HoldenLab/LifeHack/Main Body/Parts/Camera mount (With OptoSplit).stl

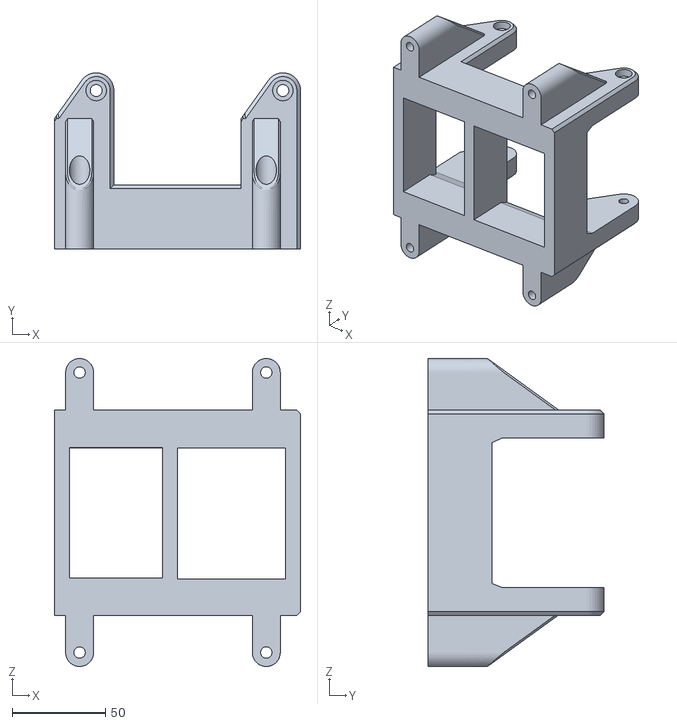
[picture p37: CAD file, 2020-11-02]
Main Body/Parts/Camera mount (With OptoSplit).stl
131.9 x 94.5 x 165.0
