HoldenLab/LifeHack/Main Body/Parts/Focus Shifter/Arduino Box/Arduino Box Bottom.stl

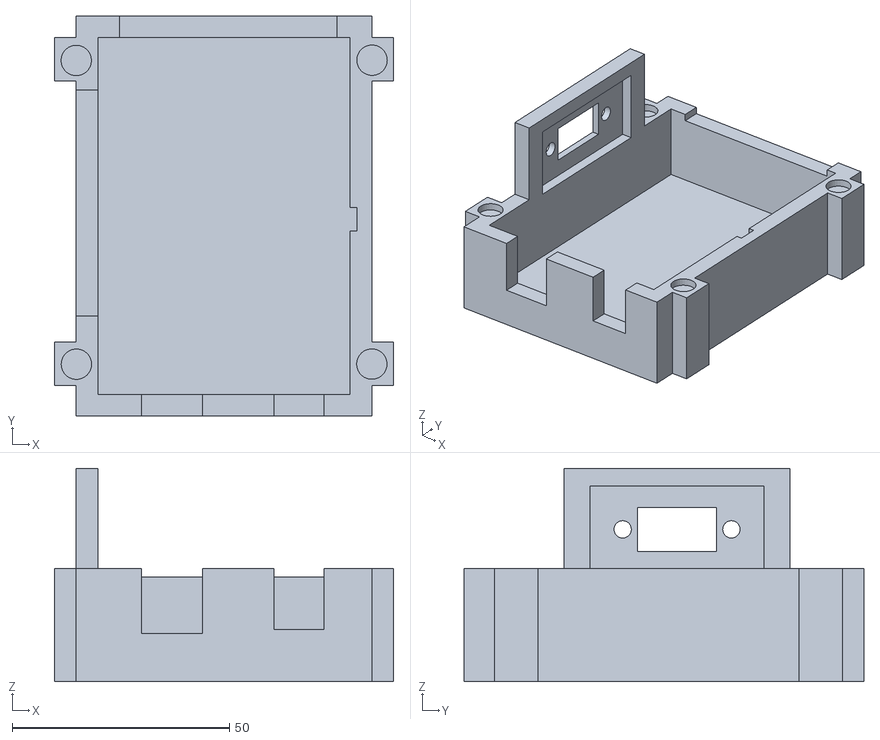
[picture p38: CAD file, 2020-12-13]
Main Body/Parts/Focus Shifter/Arduino Box/Arduino Box Bottom.stl
78.0 x 92.0 x 49.0
