HoldenLab/LifeHack/Main Body/Parts/Focus Shifter/Controller Box/Controller Box Bottom.stl

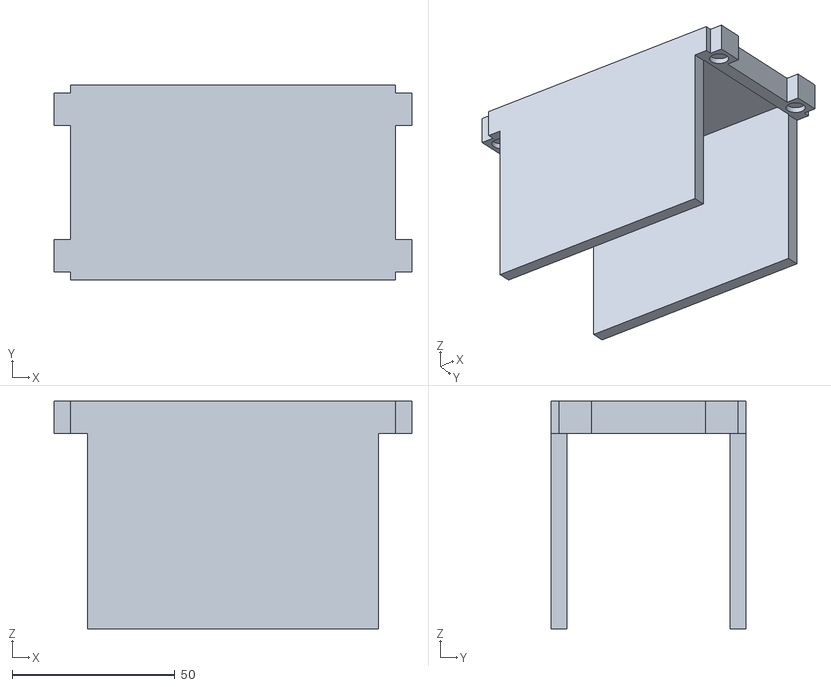
[picture p39: CAD file, 2020-12-13]
Main Body/Parts/Focus Shifter/Controller Box/Controller Box Bottom.stl
110.0 x 60.0 x 70.0
