HoldenLab/LifeHack/Excitation Module/Parts/Diode Laser Mount - 3D Print.stl

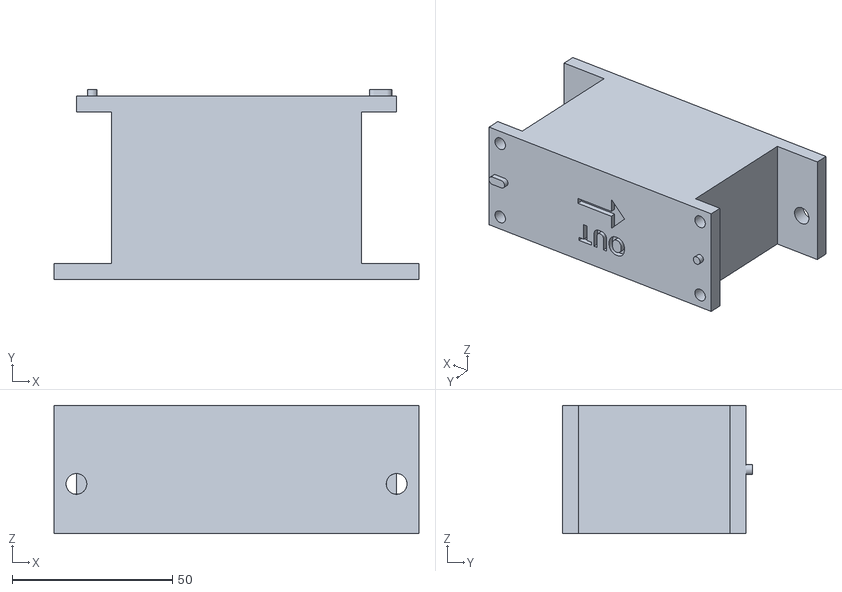
[picture p40: CAD file, 2020-10-29]
Excitation Module/Parts/Diode Laser Mount - 3D Print.stl
114.0 x 59.2 x 40.0
