HoldenLab/LifeHack/Incubation Box/Parts/Incubation-Chamber-Front-Middle-Door-Mount1.dxf

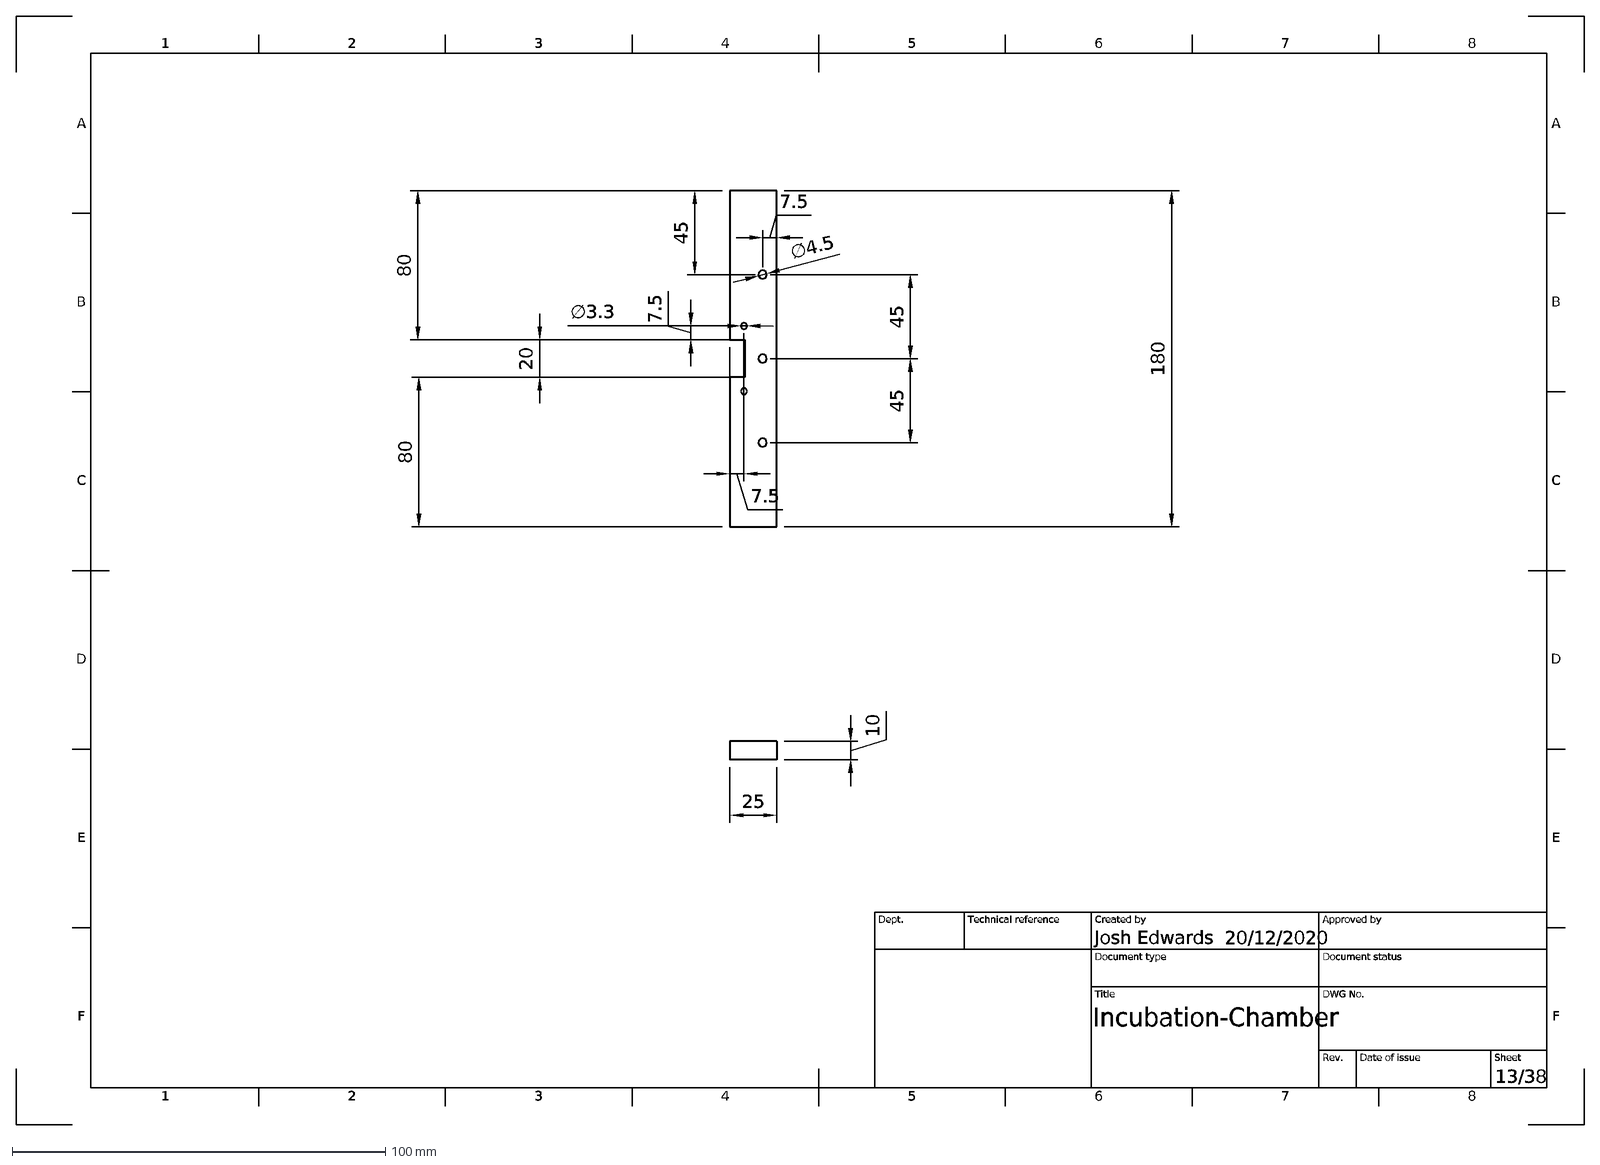
[picture p41: CAD file, 2020-12-22]
Incubation Box/Parts/Incubation-Chamber-Front-Middle-Door-Mount1.dxf
1
A
2
3
4
5
6
7
8
B
C
D
E
F
20/12/2020
13/38
Incubation-Chamber
Josh Edwards
Dept.
Technical reference
Created by
Approved by
Document type
Document status
Title
DWG No.
Rev.
Date of issue
Sheet
25
10
20
80
180
∅4.5
45
7.5
∅3.3
