HoldenLab/LifeHack/Excitation Module/Parts/Fiber Laser Mount - 3D Print.stl

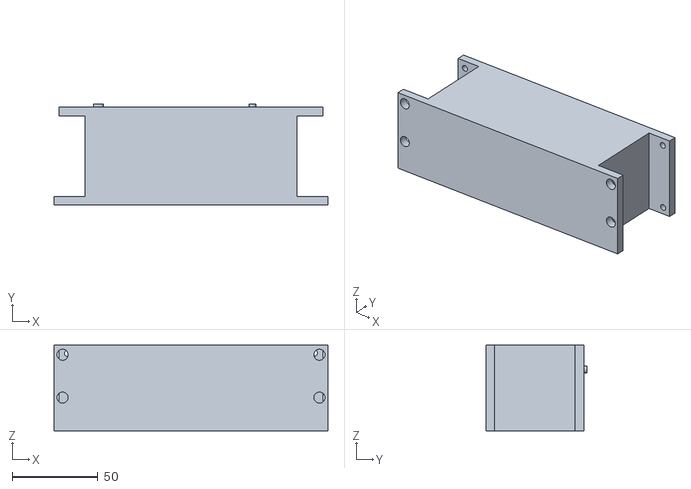
[picture p42: CAD file, 2020-10-29]
Excitation Module/Parts/Fiber Laser Mount - 3D Print.stl
160.0 x 59.2 x 50.0
