HoldenLab/LifeHack/Incubation Box/Parts/Incubation-Chamber-Left-Door-Mount3.dxf

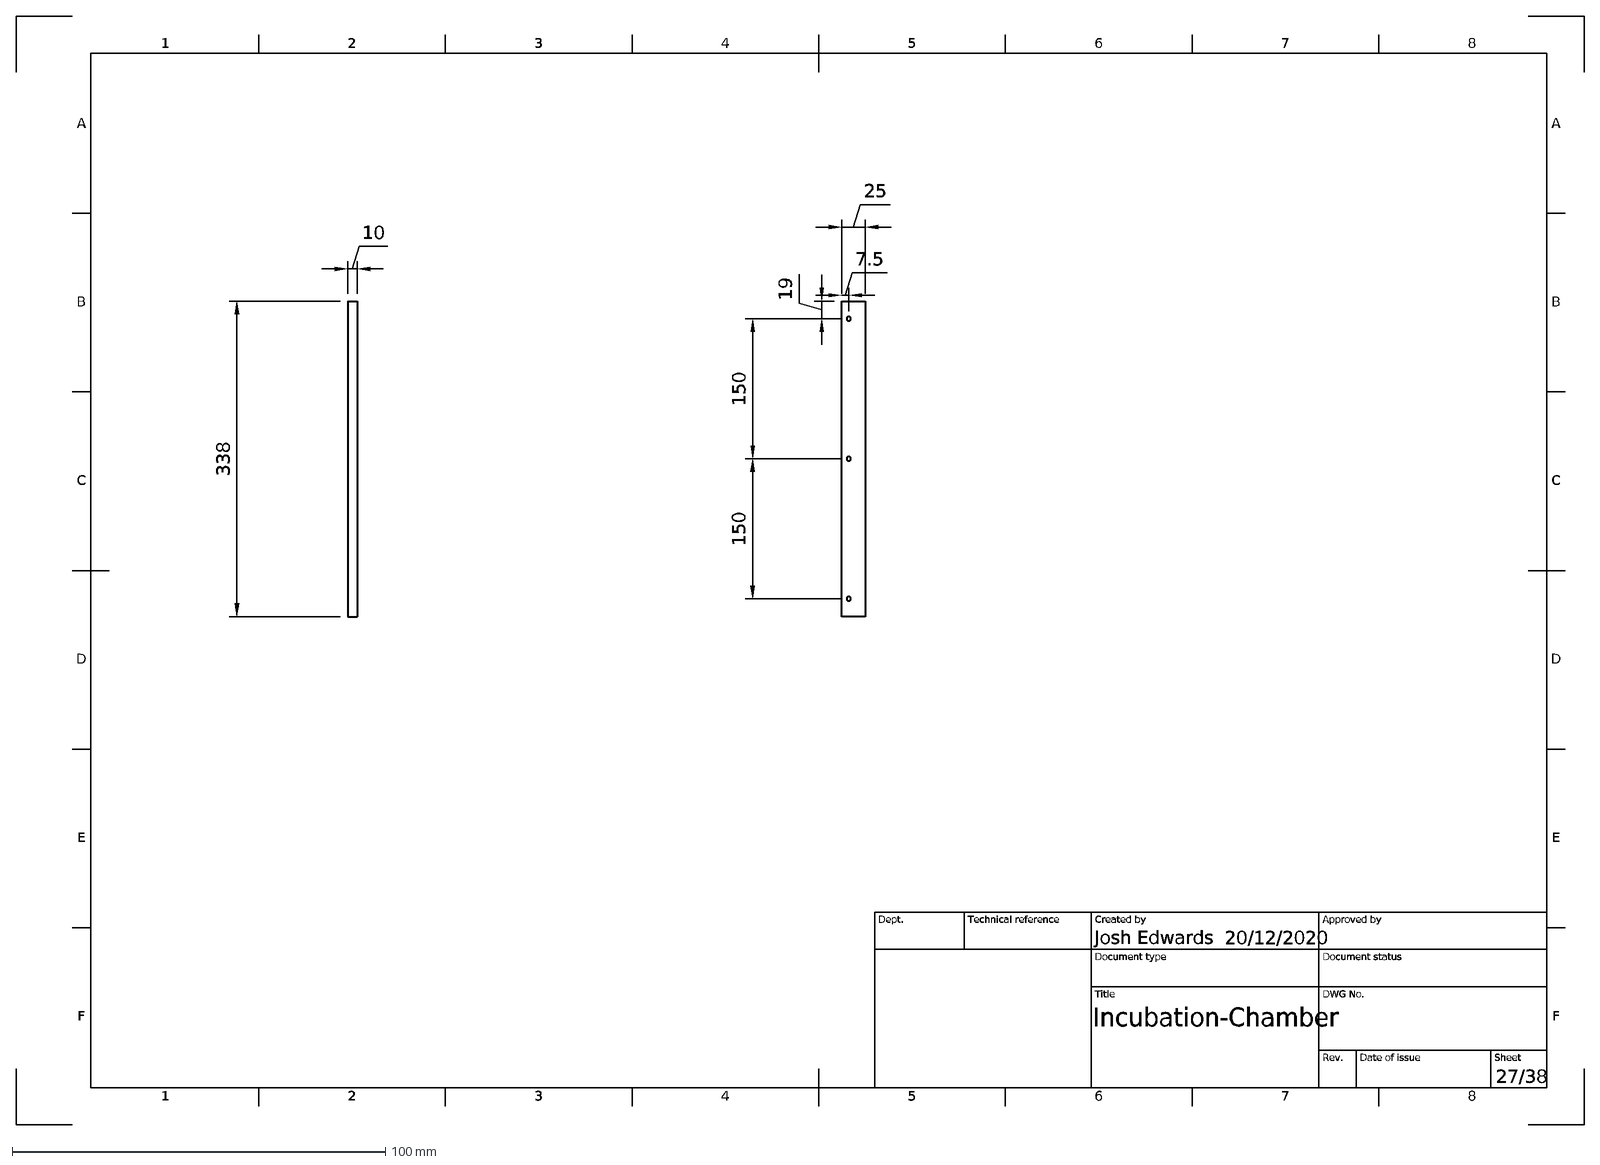
[picture p43: CAD file, 2020-12-22]
Incubation Box/Parts/Incubation-Chamber-Left-Door-Mount3.dxf
1
A
2
3
4
5
6
7
8
B
C
D
E
F
20/12/2020
27/38
Incubation-Chamber
Josh Edwards
Dept.
Technical reference
Created by
Approved by
Document type
Document status
Title
DWG No.
Rev.
Date of issue
Sheet
338
10
25
19
7.5
150
