HoldenLab/LifeHack/Incubation Box/Parts/Incubation-Chamber-Left-Camera-Port.dxf

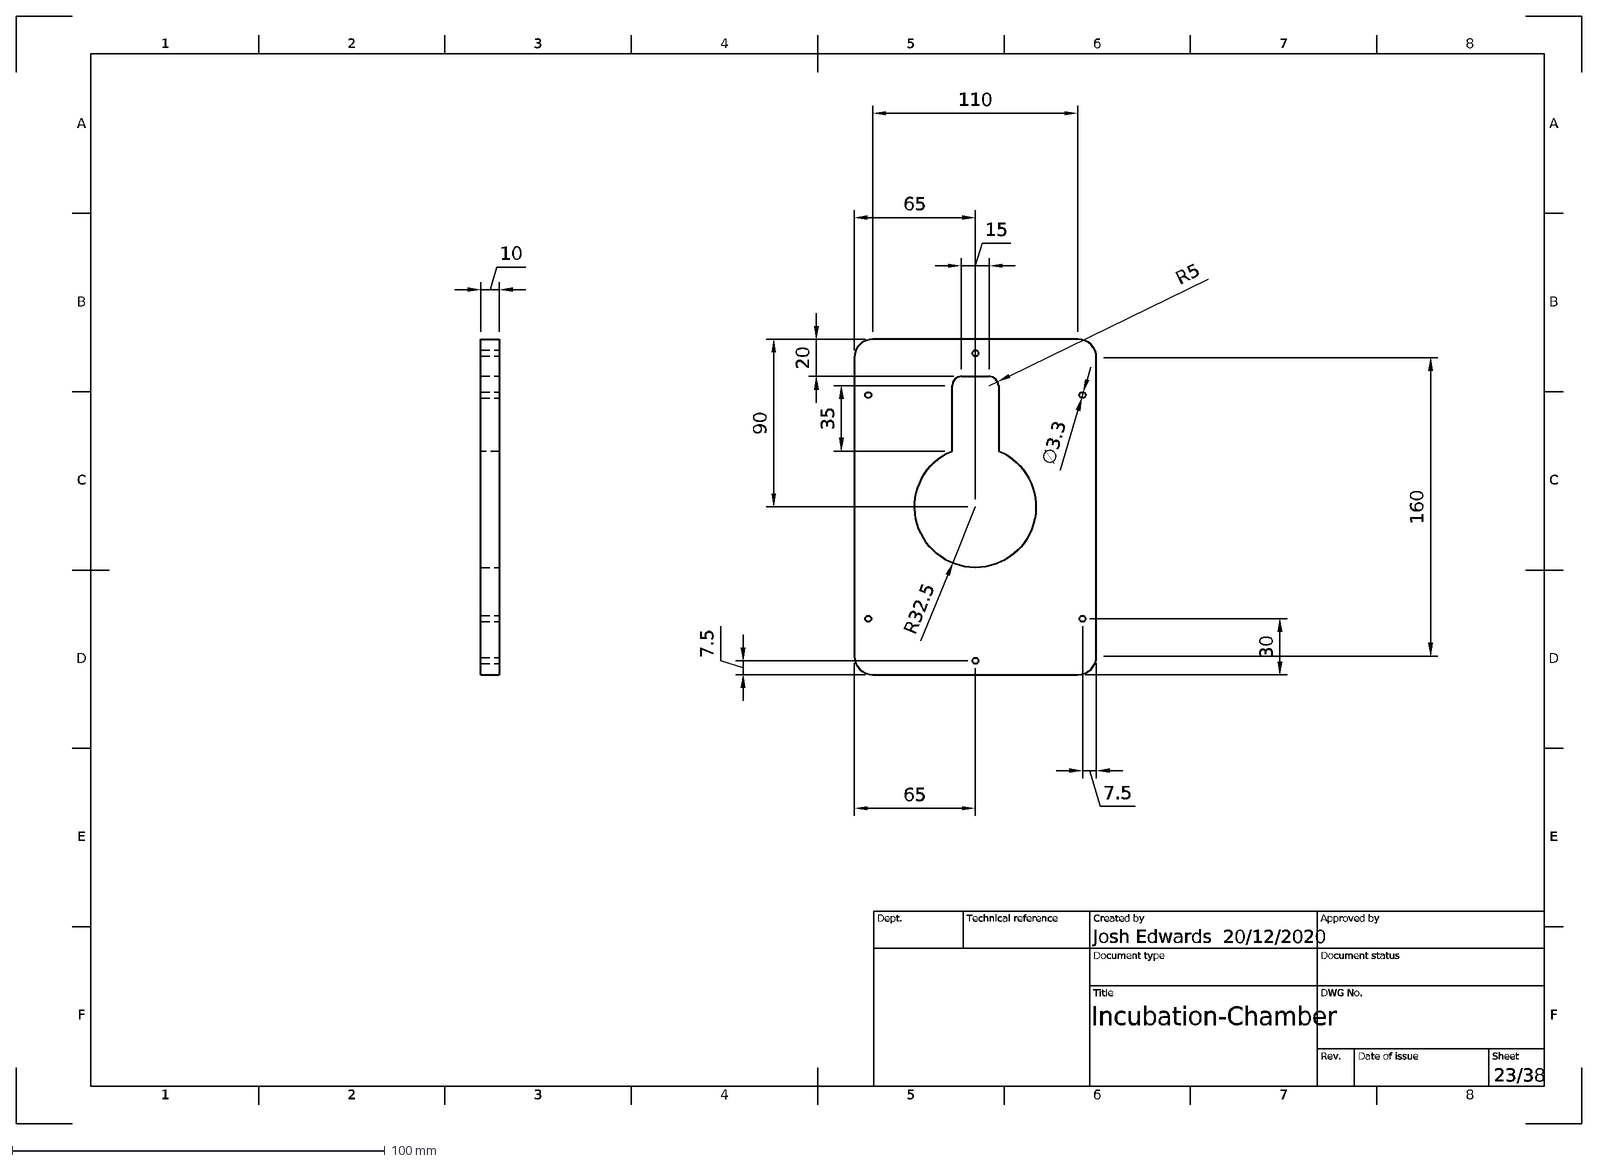
[picture p44: CAD file, 2020-12-22]
Incubation Box/Parts/Incubation-Chamber-Left-Camera-Port.dxf
1
A
2
3
4
5
6
7
8
B
C
D
E
F
20/12/2020
23/38
Incubation-Chamber
Josh Edwards
Dept.
Technical reference
Created by
Approved by
Document type
Document status
Title
DWG No.
Rev.
Date of issue
Sheet
10
110
160
7.5
30
∅3.3
R32.5
65
15
R5
90
20
35
