HoldenLab/LifeHack/Incubation Box/Parts/Incubation-Chamber-Front-Bottom-Door.dxf

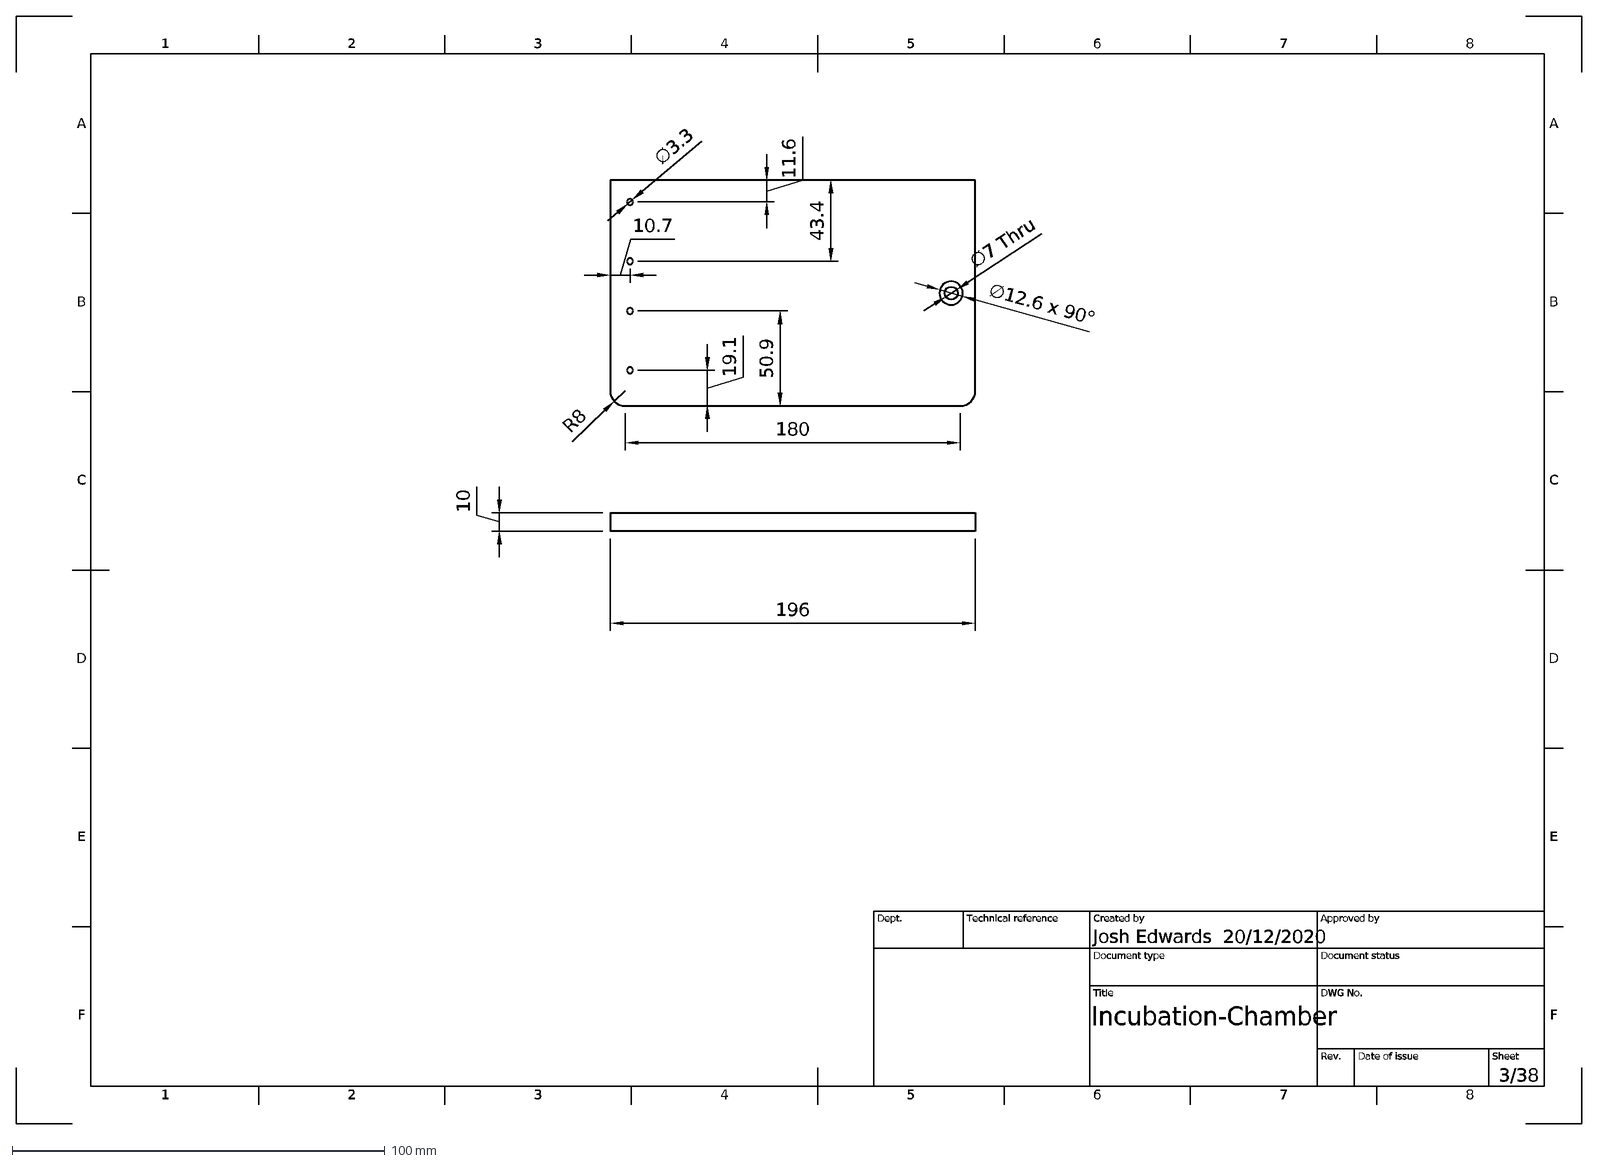
[picture p45: CAD file, 2020-12-22]
Incubation Box/Parts/Incubation-Chamber-Front-Bottom-Door.dxf
1
A
2
3
4
5
6
7
8
B
C
D
E
F
20/12/2020
3/38
Incubation-Chamber
Josh Edwards
Dept.
Technical reference
Created by
Approved by
Document type
Document status
Title
DWG No.
Rev.
Date of issue
Sheet
196
10
180
R8
∅7 Thru
∅12.6 x 90°
∅3.3
10.7
19.1
50.9
11.6
43.4
