HoldenLab/LifeHack/Incubation Box/Parts/Incubation-Chamber-Front-Bottom-Door-Mount1.dxf

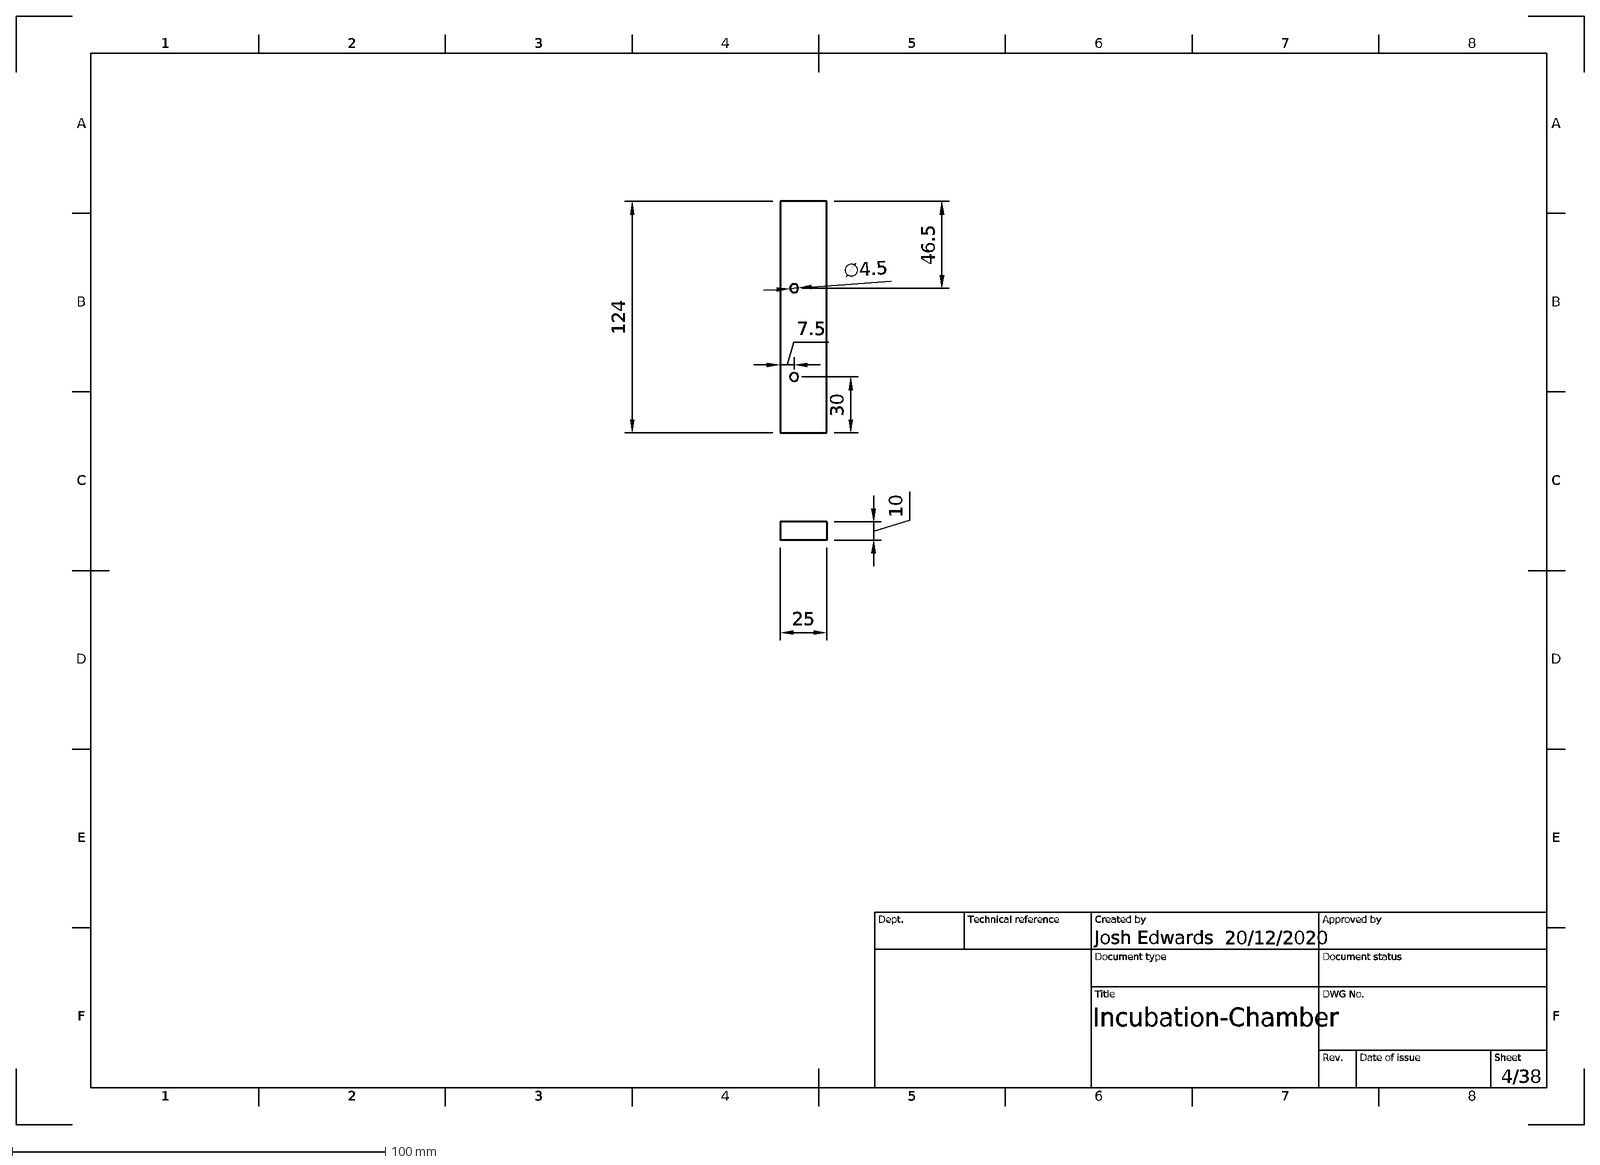
[picture p47: CAD file, 2020-12-22]
Incubation Box/Parts/Incubation-Chamber-Front-Bottom-Door-Mount1.dxf
1
A
2
3
4
5
6
7
8
B
C
D
E
F
20/12/2020
4/38
Incubation-Chamber
Josh Edwards
Dept.
Technical reference
Created by
Approved by
Document type
Document status
Title
DWG No.
Rev.
Date of issue
Sheet
124
25
10
∅4.5
7.5
30
46.5
