HoldenLab/LifeHack/Incubation Box/Parts/Incubation-Chamber-Right-Door.dxf

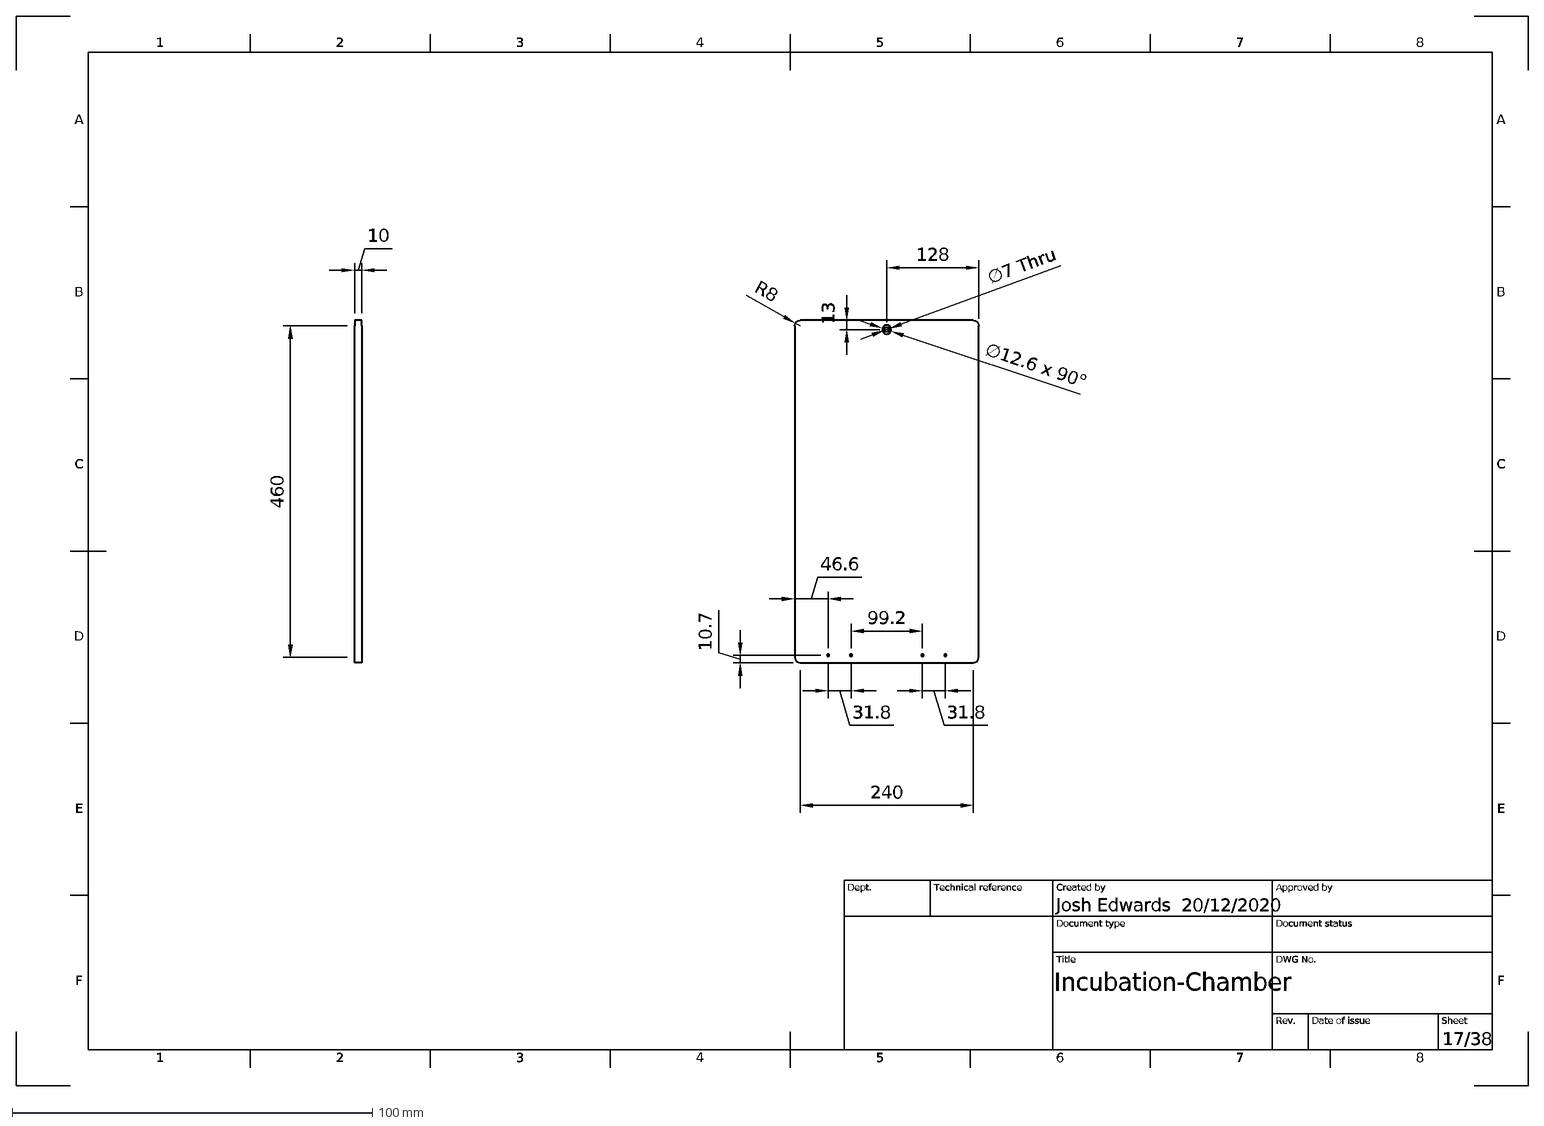
[picture p48: CAD file, 2020-12-22]
Incubation Box/Parts/Incubation-Chamber-Right-Door.dxf
1
A
2
3
4
5
6
7
8
B
C
D
E
F
20/12/2020
17/38
Incubation-Chamber
Josh Edwards
Dept.
Technical reference
Created by
Approved by
Document type
Document status
Title
DWG No.
Rev.
Date of issue
Sheet
460
10
R8
∅12.6 x 90°
∅7 Thru
13
128
10.7
46.6
31.8
99.2
240
