HoldenLab/LifeHack/Incubation Box/Parts/Incubation-Chamber-Left-Panel.dxf

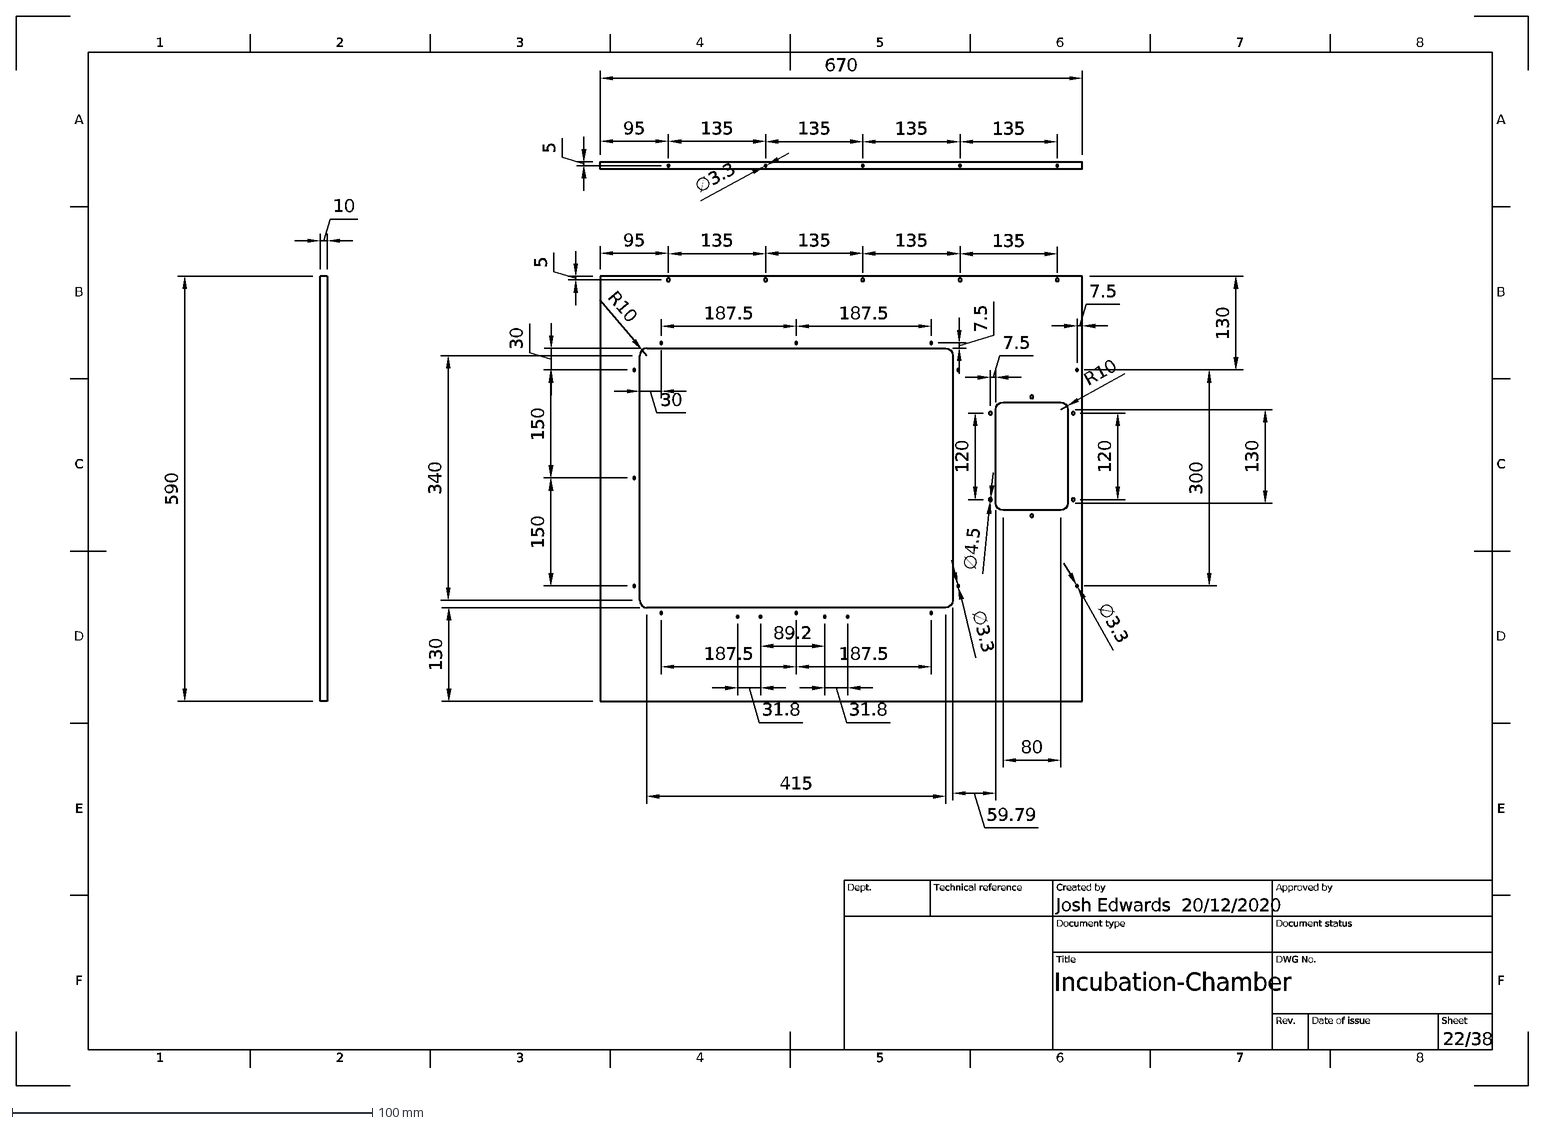
[picture p49: CAD file, 2020-12-22]
Incubation Box/Parts/Incubation-Chamber-Left-Panel.dxf
1
A
2
3
4
5
6
7
8
B
C
D
E
F
20/12/2020
22/38
Incubation-Chamber
Josh Edwards
Dept.
Technical reference
Created by
Approved by
Document type
Document status
Title
DWG No.
Rev.
Date of issue
Sheet
590
10
670
95
135
∅3.3
130
415
340
R10
59.79
80
120
300
7.5
∅4.5
187.5
30
150
31.8
89.2
