HoldenLab/LifeHack/Incubation Box/Parts/Incubation-Chamber-Front-Bottom-Door-Mount4.dxf

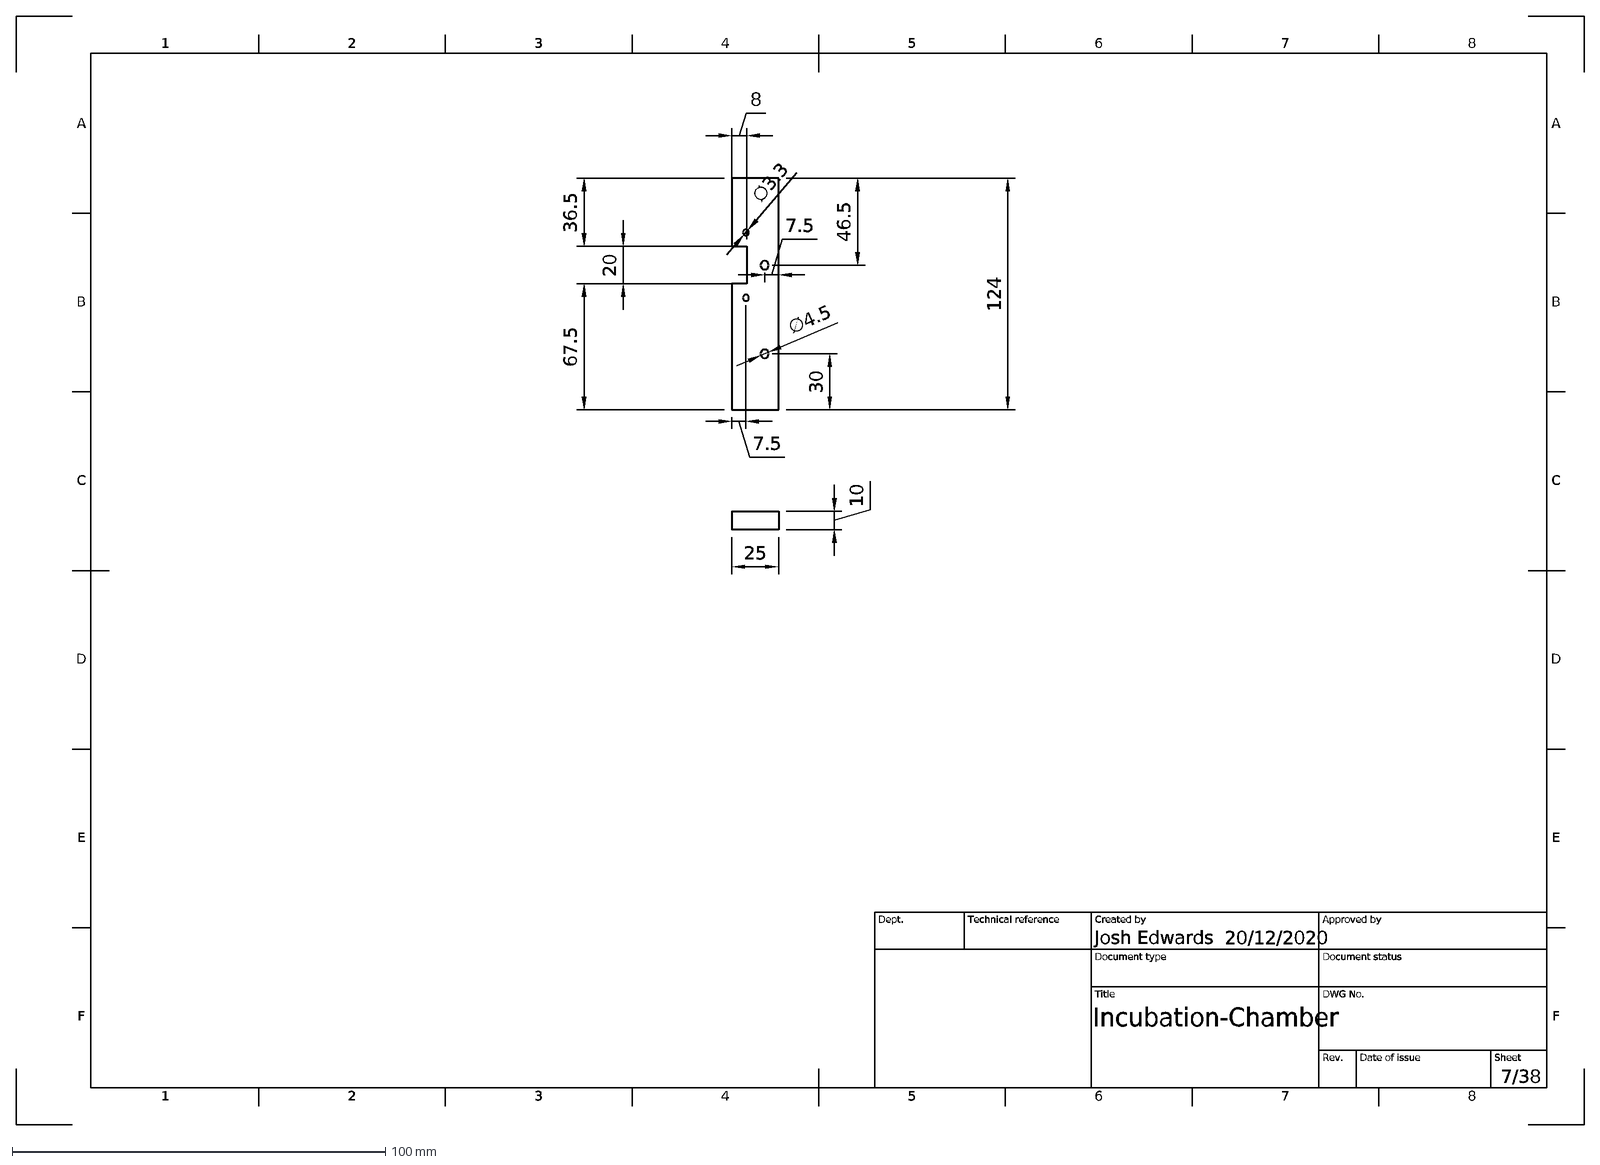
[picture p51: CAD file, 2020-12-22]
Incubation Box/Parts/Incubation-Chamber-Front-Bottom-Door-Mount4.dxf
1
A
2
3
4
5
6
7
8
B
C
D
E
F
20/12/2020
7/38
Incubation-Chamber
Josh Edwards
Dept.
Technical reference
Created by
Approved by
Document type
Document status
Title
DWG No.
Rev.
Date of issue
Sheet
20
36.5
67.5
124
10
25
7.5
30
46.5
∅3.3
∅4.5
