HoldenLab/LifeHack/Incubation Box/Parts/Incubation-Chamber-Front-Bottom-Door-Mount3.dxf

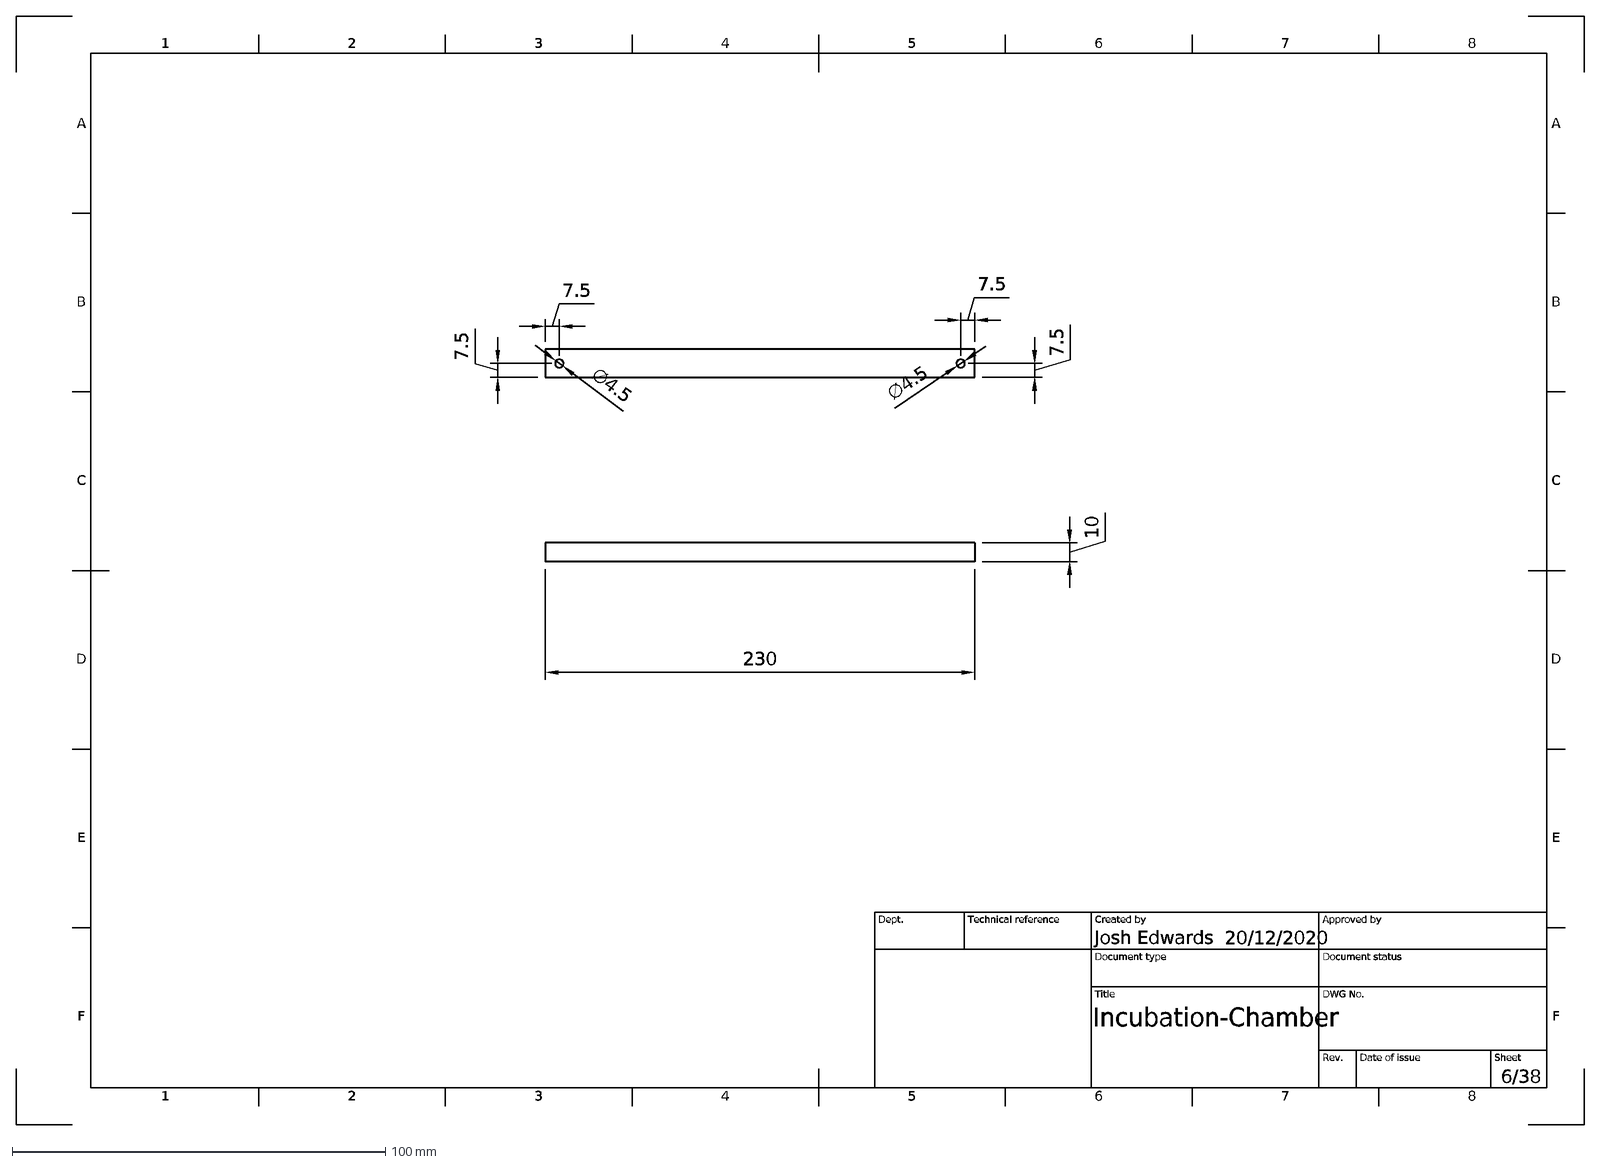
[picture p55: CAD file, 2020-12-22]
Incubation Box/Parts/Incubation-Chamber-Front-Bottom-Door-Mount3.dxf
1
A
2
3
4
5
6
7
8
B
C
D
E
F
20/12/2020
6/38
Incubation-Chamber
Josh Edwards
Dept.
Technical reference
Created by
Approved by
Document type
Document status
Title
DWG No.
Rev.
Date of issue
Sheet
230
10
7.5
∅4.5
