HoldenLab/LifeHack/Incubation Box/Parts/Incubation-Chamber-Back-Excitation-Hatch.dxf

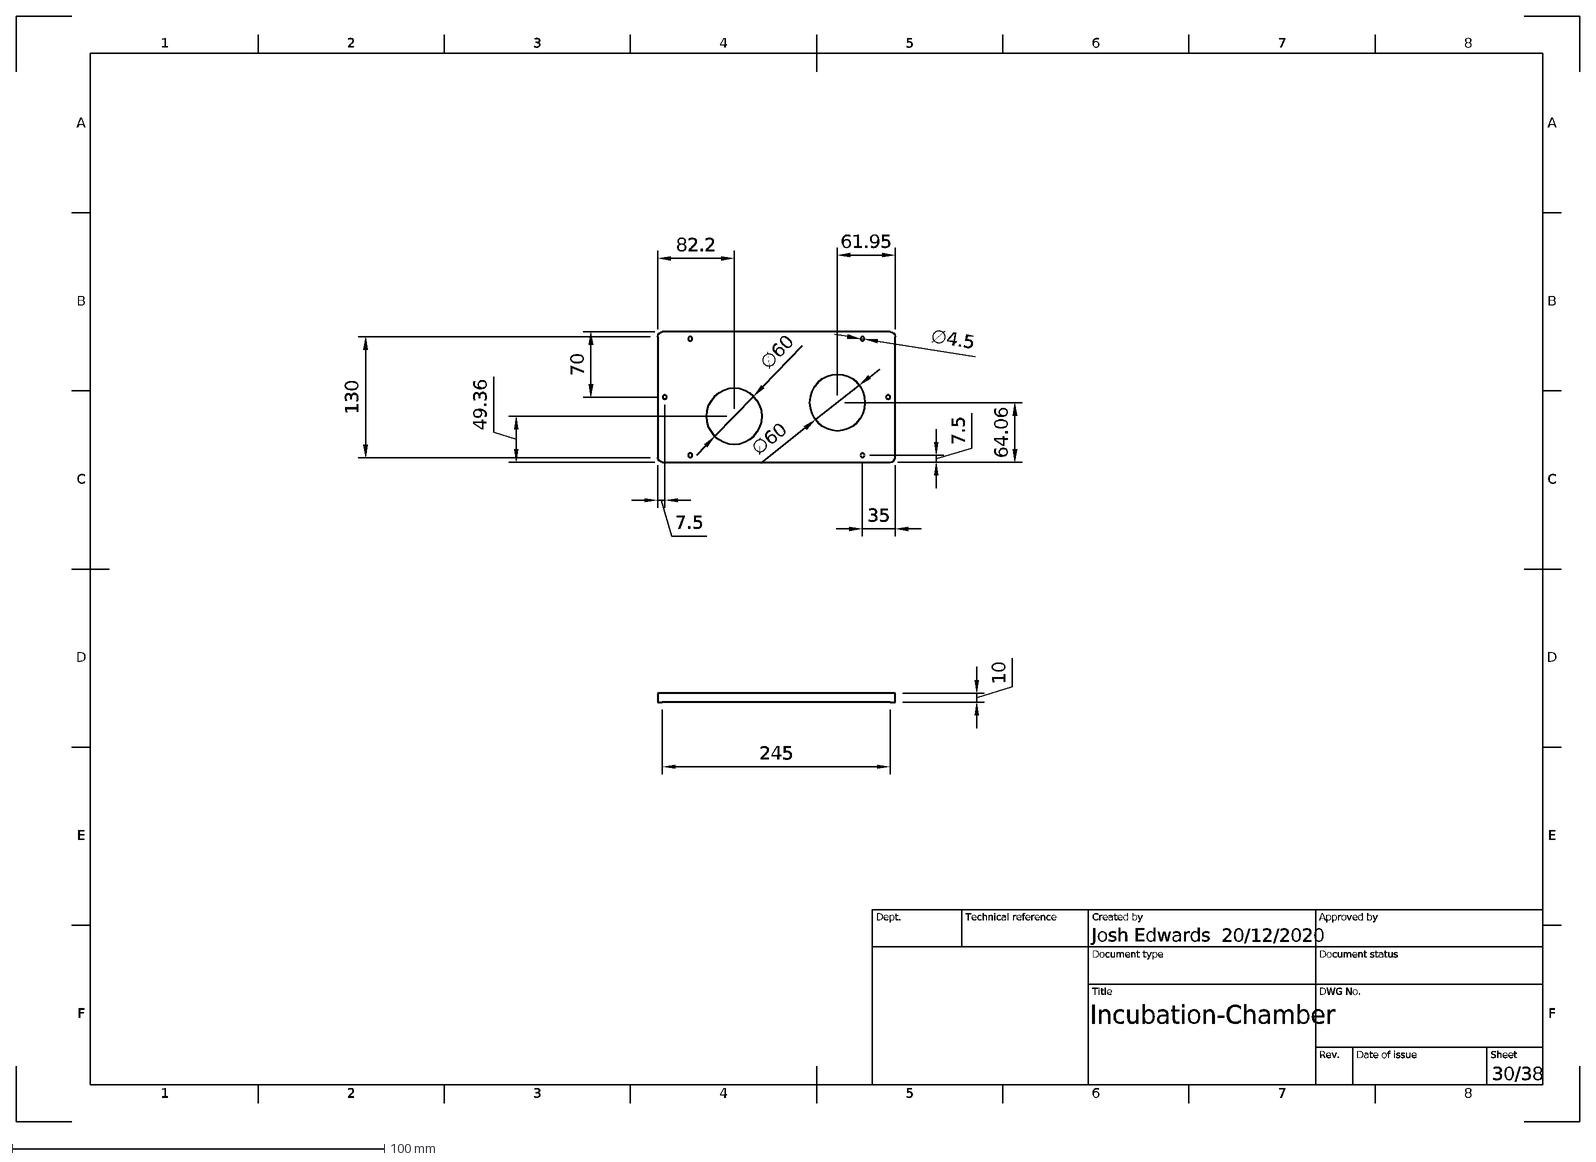
[picture p56: CAD file, 2020-12-22]
Incubation Box/Parts/Incubation-Chamber-Back-Excitation-Hatch.dxf
1
A
2
3
4
5
6
7
8
B
C
D
E
F
20/12/2020
30/38
Incubation-Chamber
Josh Edwards
Dept.
Technical reference
Created by
Approved by
Document type
Document status
Title
DWG No.
Rev.
Date of issue
Sheet
245
10
130
70
7.5
∅60
82.2
61.95
64.06
49.36
35
∅4.5
