HoldenLab/LifeHack/Incubation Box/Parts/Incubation-Chamber-Front-Panel.dxf

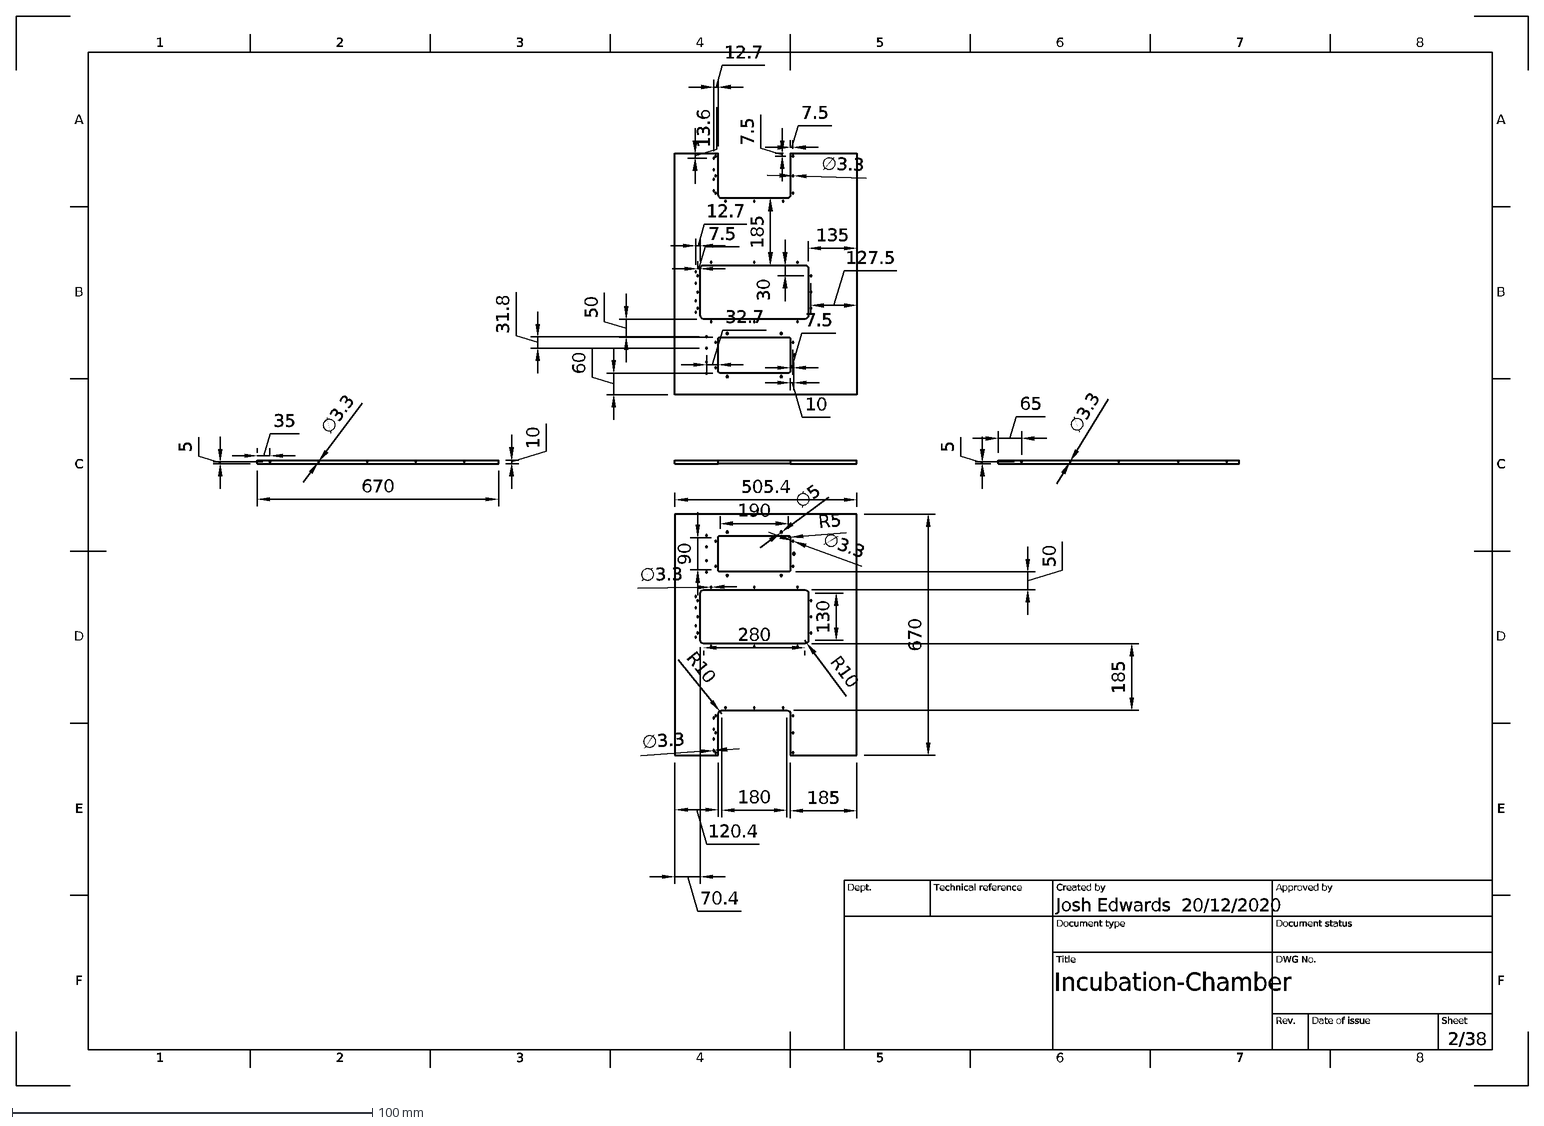
[picture p57: CAD file, 2020-12-22]
Incubation Box/Parts/Incubation-Chamber-Front-Panel.dxf
1
A
2
3
4
5
6
7
8
B
C
D
E
F
20/12/2020
2/38
Incubation-Chamber
Josh Edwards
Dept.
Technical reference
Created by
Approved by
Document type
Document status
Title
DWG No.
Rev.
Date of issue
Sheet
505.4
670
10
∅3.3
180
R10
185
120.4
130
280
R5
∅5
190
90
135
127.5
30
7.5
12.7
50
60
32.7
31.8
35
65
13.6
70.4
