HoldenLab/LifeHack/Incubation Box/Parts/Incubation-Chamber-Front-Window-Cover.dxf

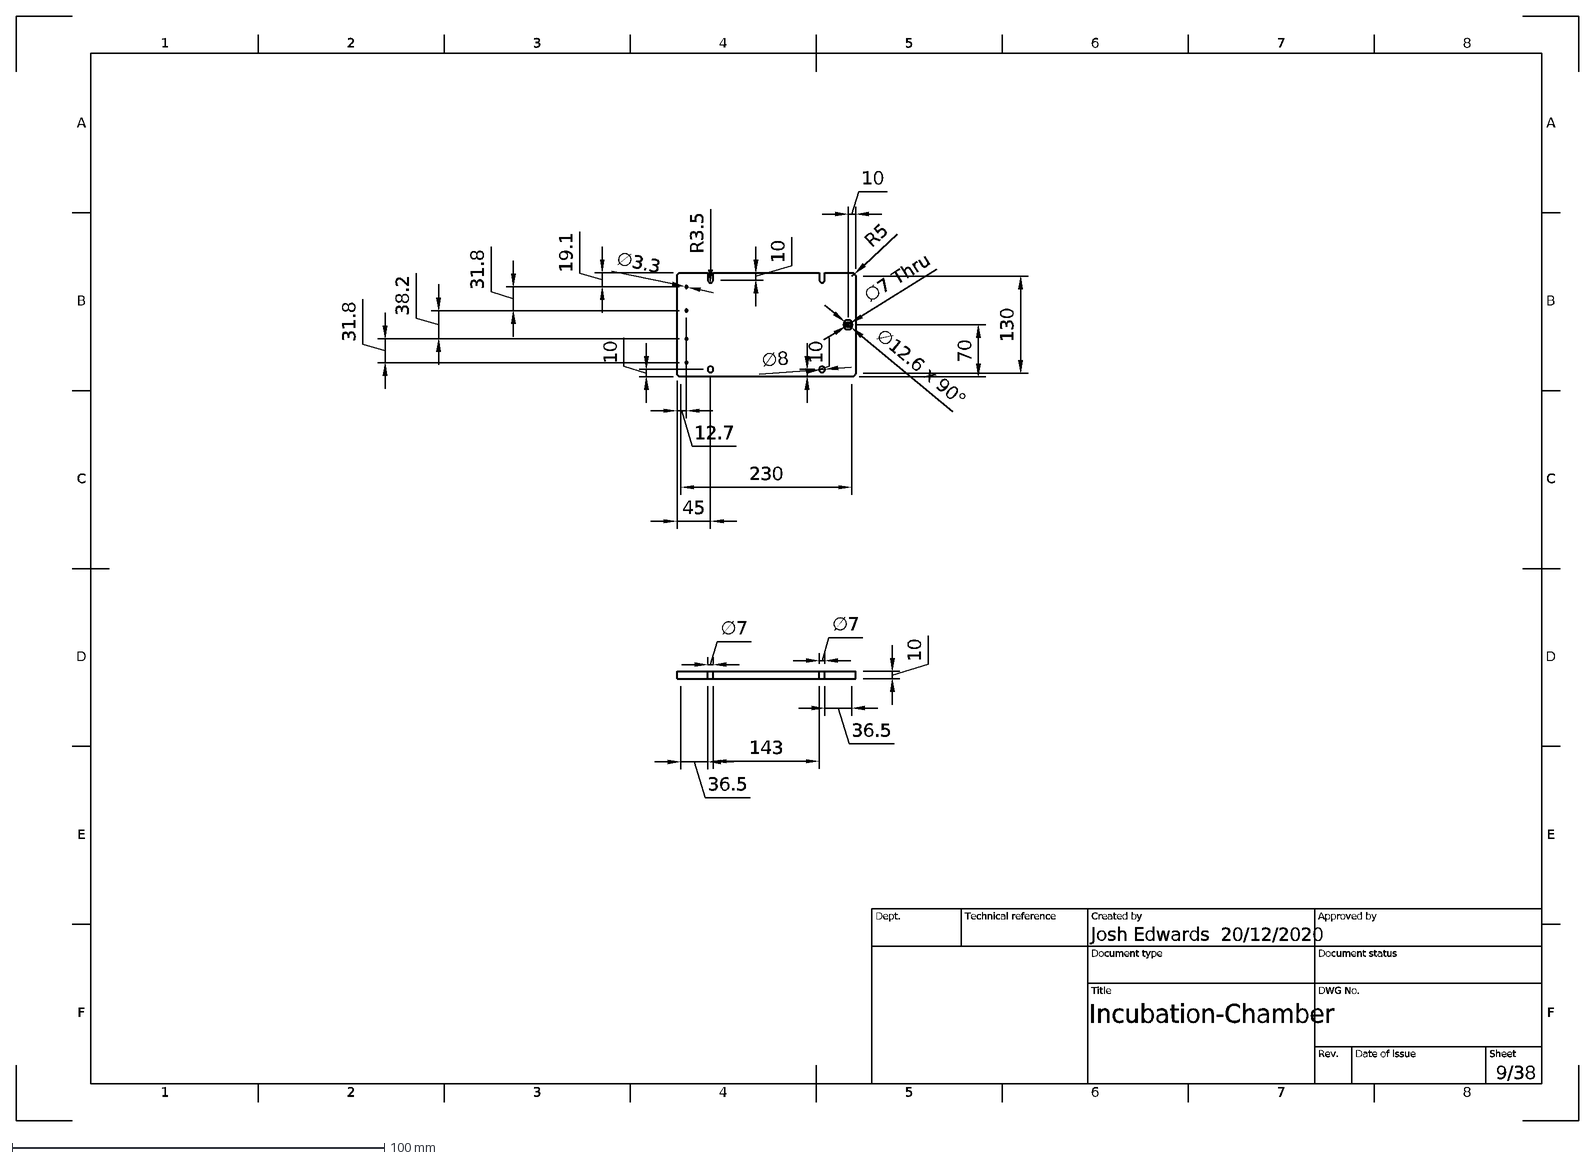
[picture p59: CAD file, 2020-12-22]
Incubation Box/Parts/Incubation-Chamber-Front-Window-Cover.dxf
1
A
2
3
4
5
6
7
8
B
C
D
E
F
20/12/2020
9/38
Incubation-Chamber
Josh Edwards
Dept.
Technical reference
Created by
Approved by
Document type
Document status
Title
DWG No.
Rev.
Date of issue
Sheet
143
36.5
∅7
10
R5
∅7 Thru
∅12.6 x 90°
70
∅8
∅3.3
R3.5
19.1
12.7
31.8
38.2
230
130
45
