HoldenLab/LifeHack/Incubation Box/Parts/Incubation-Chamber-Top-Hatch.dxf

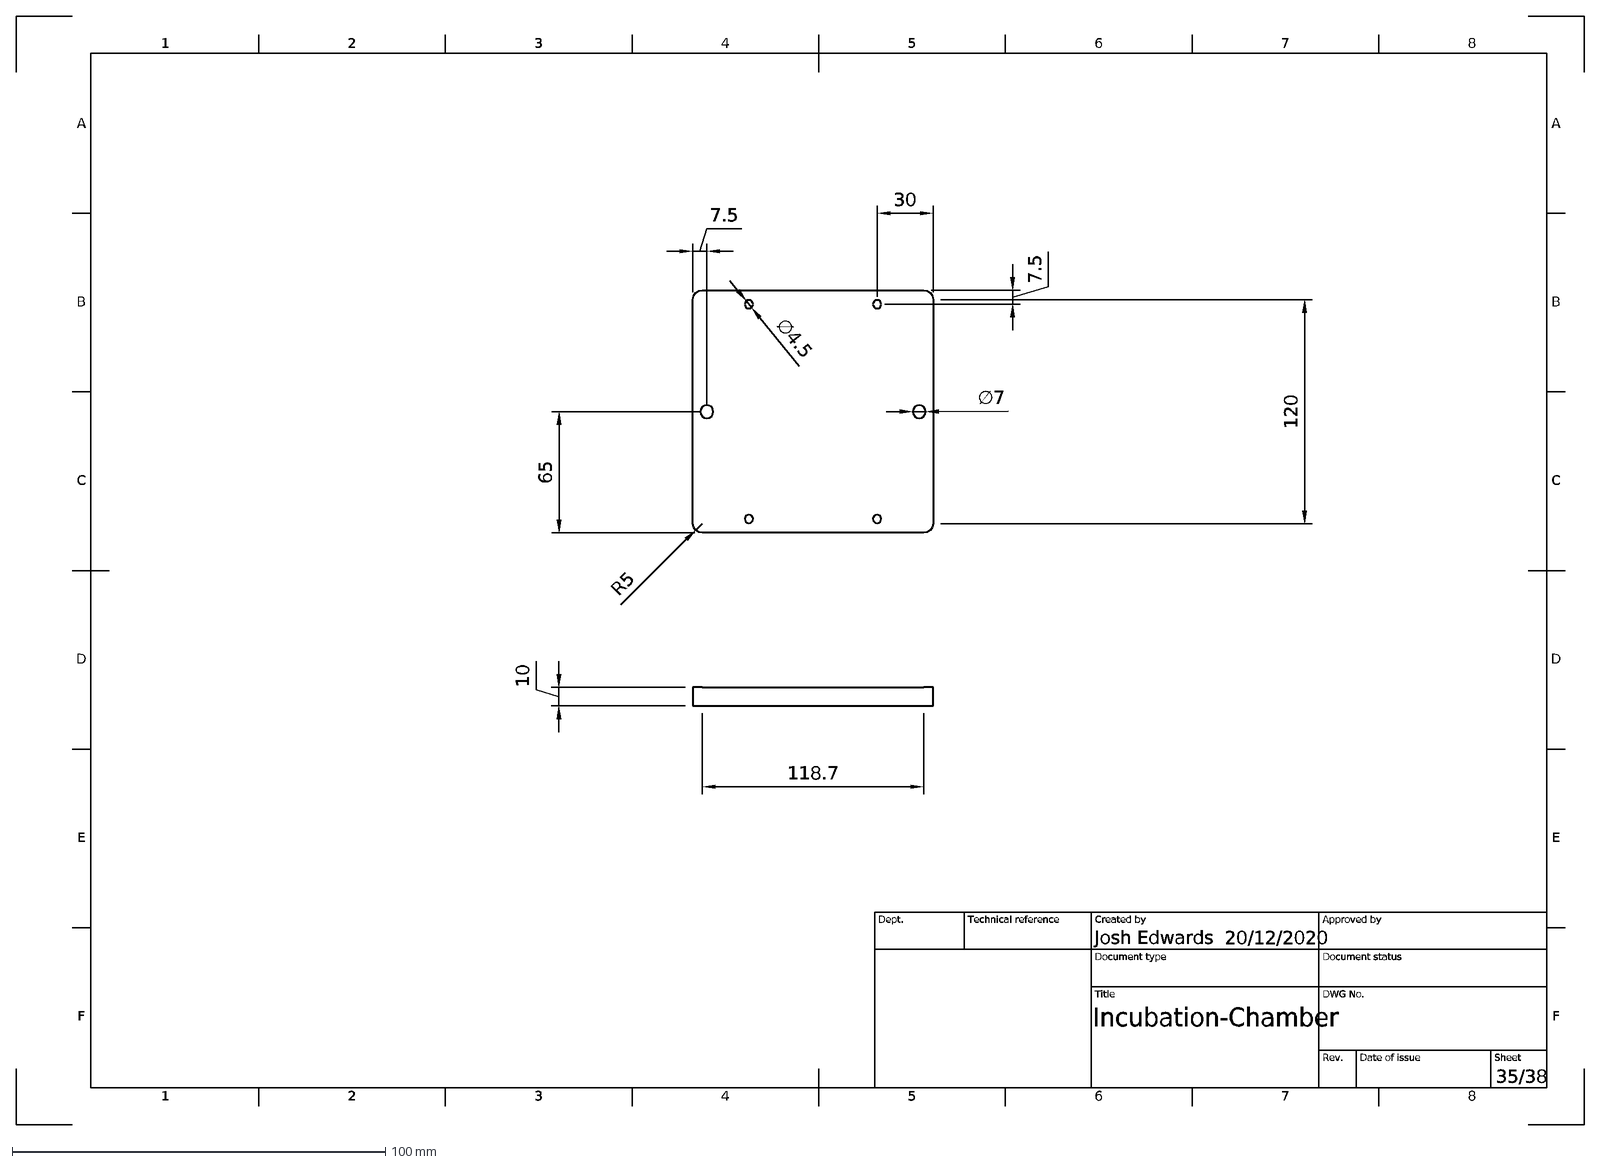
[picture p60: CAD file, 2020-12-22]
Incubation Box/Parts/Incubation-Chamber-Top-Hatch.dxf
1
A
2
3
4
5
6
7
8
B
C
D
E
F
20/12/2020
35/38
Incubation-Chamber
Josh Edwards
Dept.
Technical reference
Created by
Approved by
Document type
Document status
Title
DWG No.
Rev.
Date of issue
Sheet
118.7
10
R5
7.5
65
120
∅7
30
∅4.5
