HoldenLab/LifeHack/Incubation Box/Parts/Incubation-Chamber-Front-Window-Cover-Mount.dxf

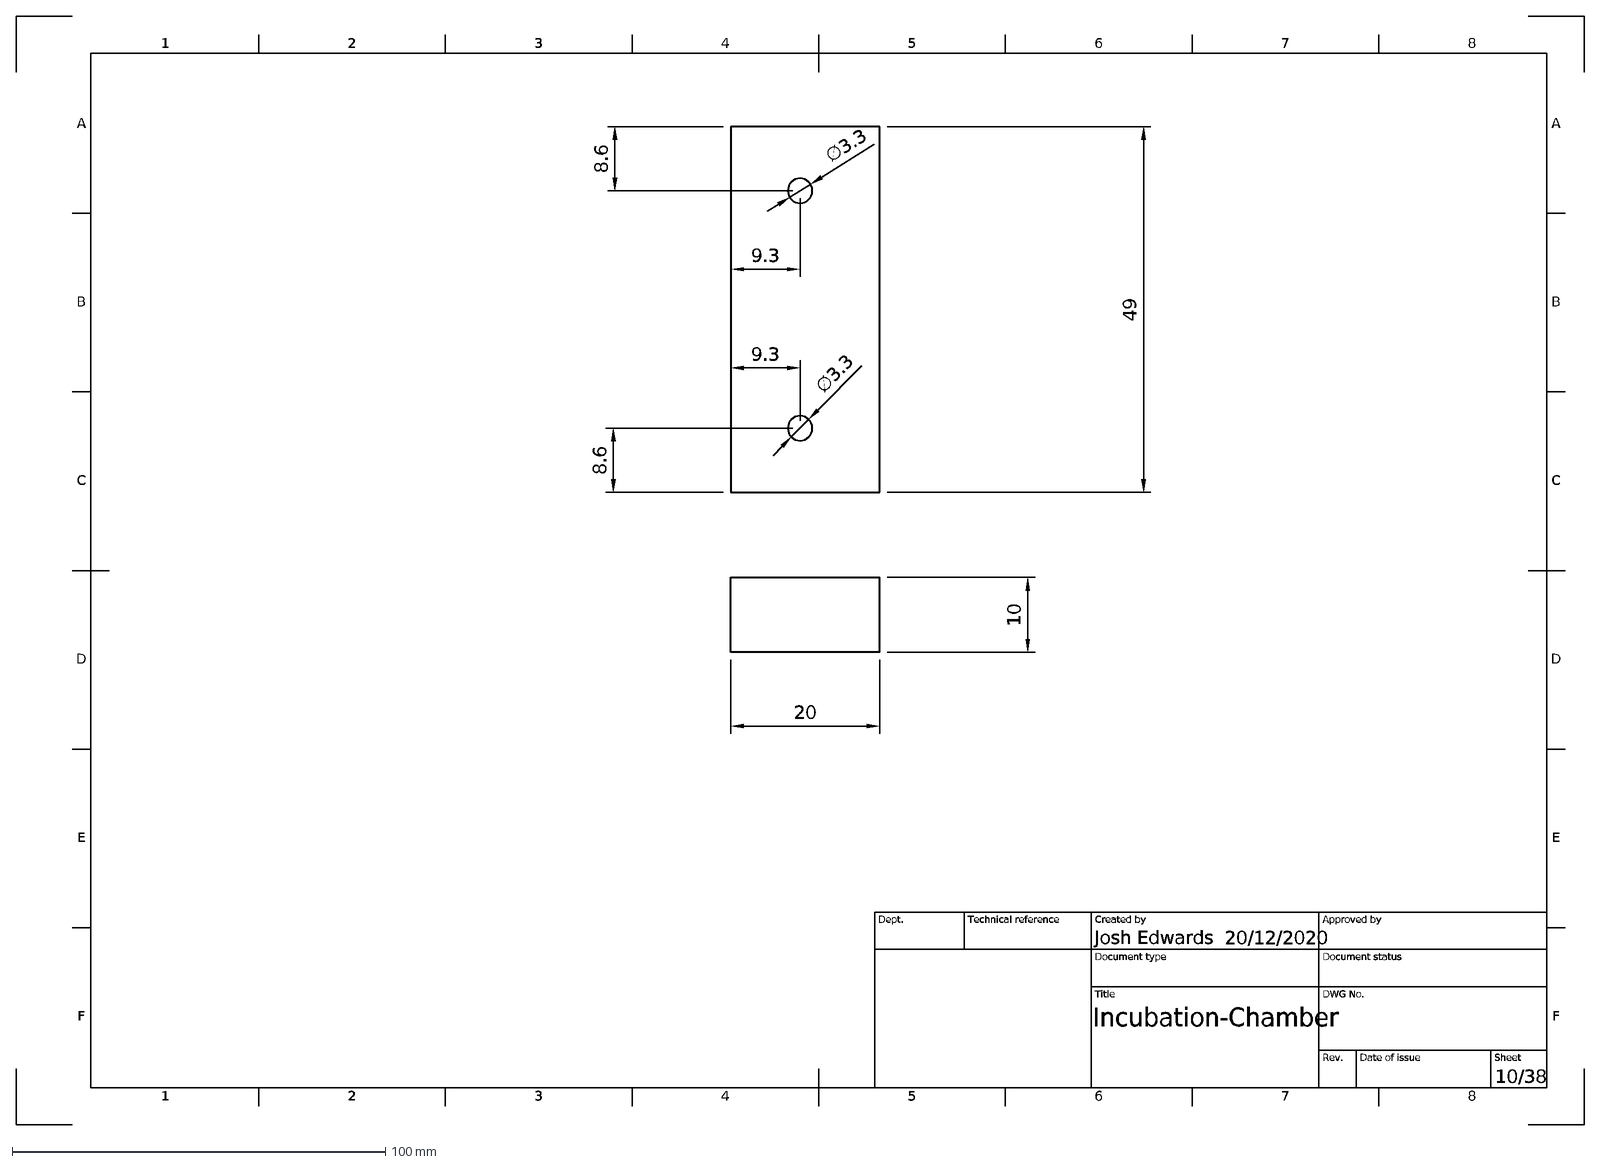
[picture p61: CAD file, 2020-12-22]
Incubation Box/Parts/Incubation-Chamber-Front-Window-Cover-Mount.dxf
1
A
2
3
4
5
6
7
8
B
C
D
E
F
20/12/2020
10/38
Incubation-Chamber
Josh Edwards
Dept.
Technical reference
Created by
Approved by
Document type
Document status
Title
DWG No.
Rev.
Date of issue
Sheet
20
10
∅3.3
8.6
9.3
49
