HoldenLab/LifeHack/Incubation Box/Parts/Incubation-Chamber-Right-Panel.dxf

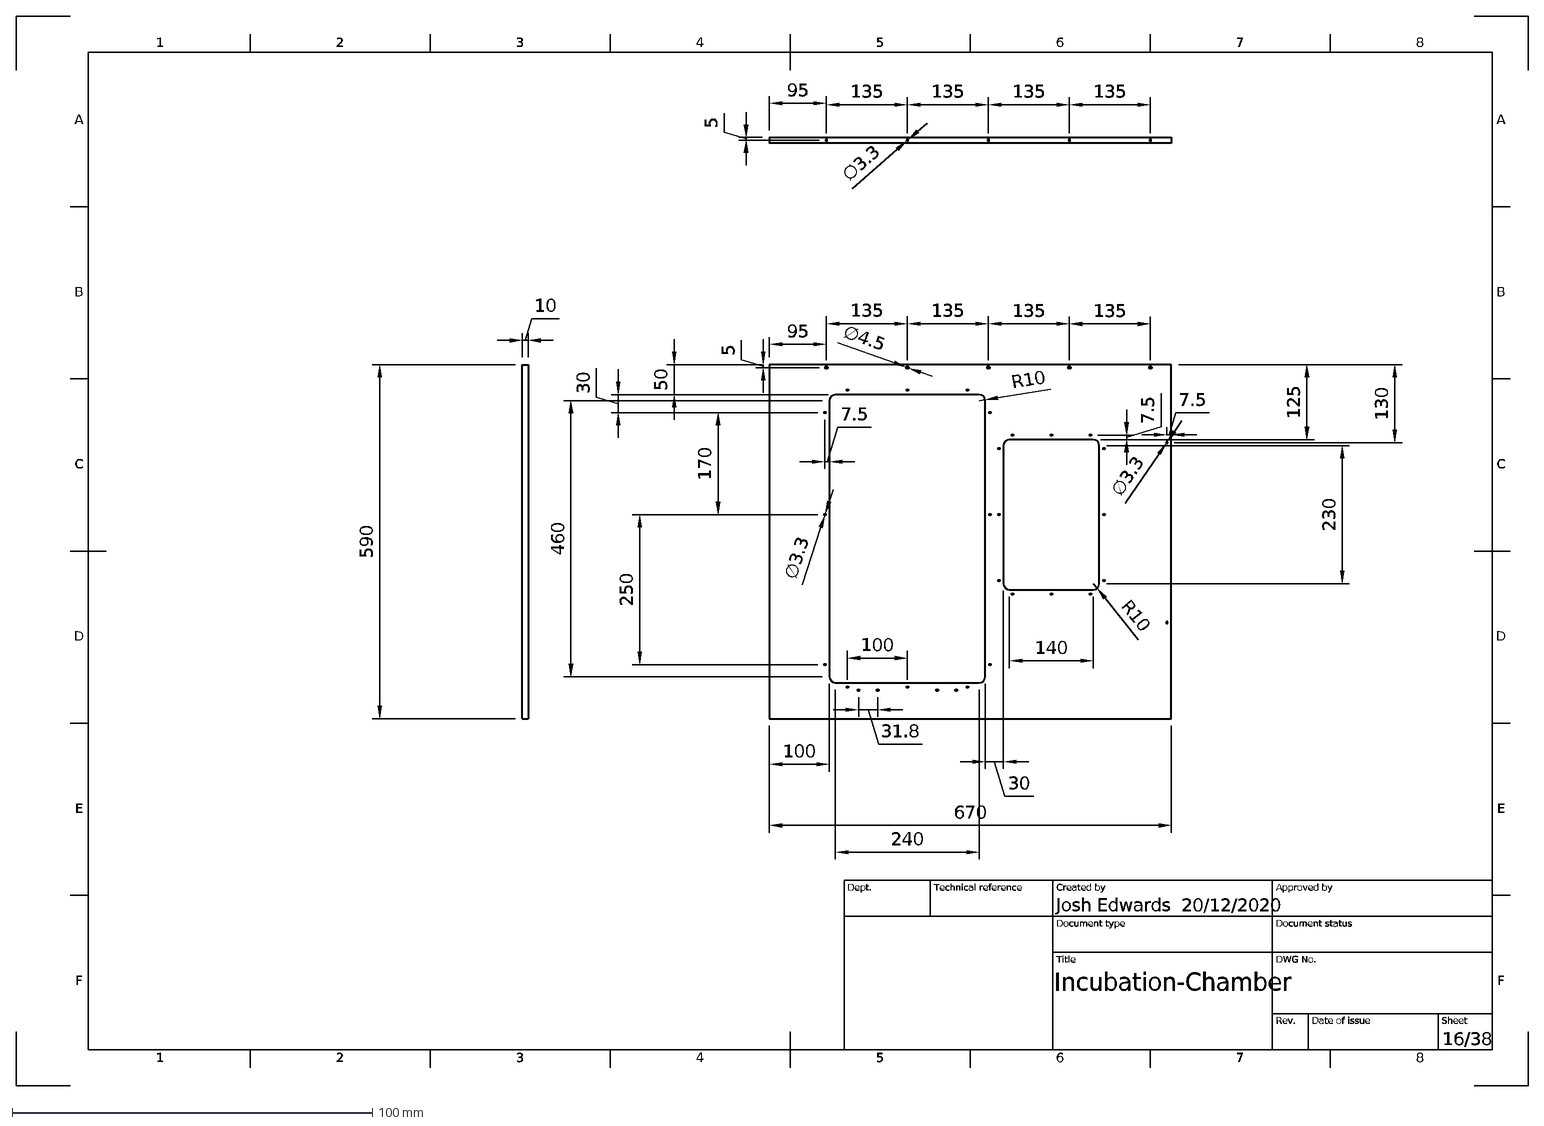
[picture p62: CAD file, 2020-12-22]
Incubation Box/Parts/Incubation-Chamber-Right-Panel.dxf
1
A
2
3
4
5
6
7
8
B
C
D
E
F
20/12/2020
16/38
Incubation-Chamber
Josh Edwards
Dept.
Technical reference
Created by
Approved by
Document type
Document status
Title
DWG No.
Rev.
Date of issue
Sheet
590
10
670
95
135
∅3.3
∅4.5
100
50
125
30
7.5
130
170
250
31.8
240
140
460
230
R10
