HoldenLab/LifeHack/Incubation Box/Parts/Incubation-Chamber-Top-Front-Diffuser-Guide.dxf

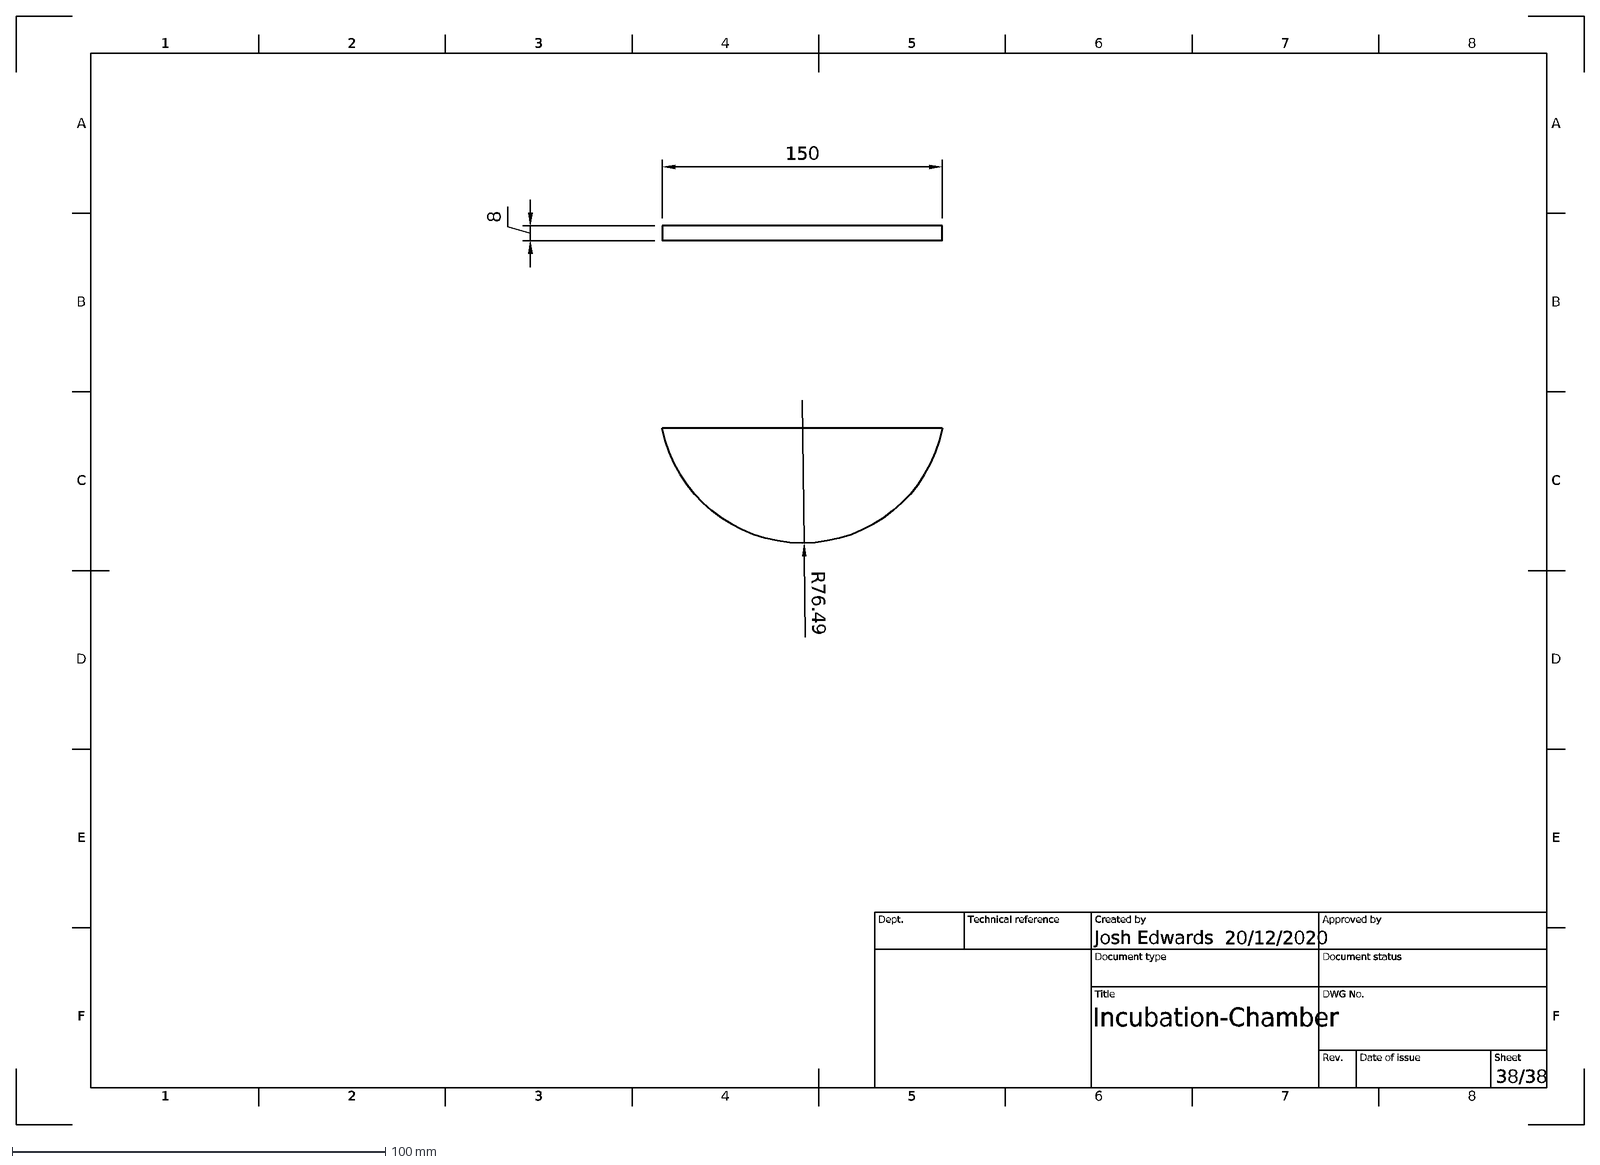
[picture p63: CAD file, 2020-12-22]
Incubation Box/Parts/Incubation-Chamber-Top-Front-Diffuser-Guide.dxf
1
A
2
3
4
5
6
7
8
B
C
D
E
F
20/12/2020
38/38
Incubation-Chamber
Josh Edwards
Dept.
Technical reference
Created by
Approved by
Document type
Document status
Title
DWG No.
Rev.
Date of issue
Sheet
150
R76.49
