HoldenLab/LifeHack/Incubation Box/Parts/Incubation-Chamber-Front-Middle-Door.dxf

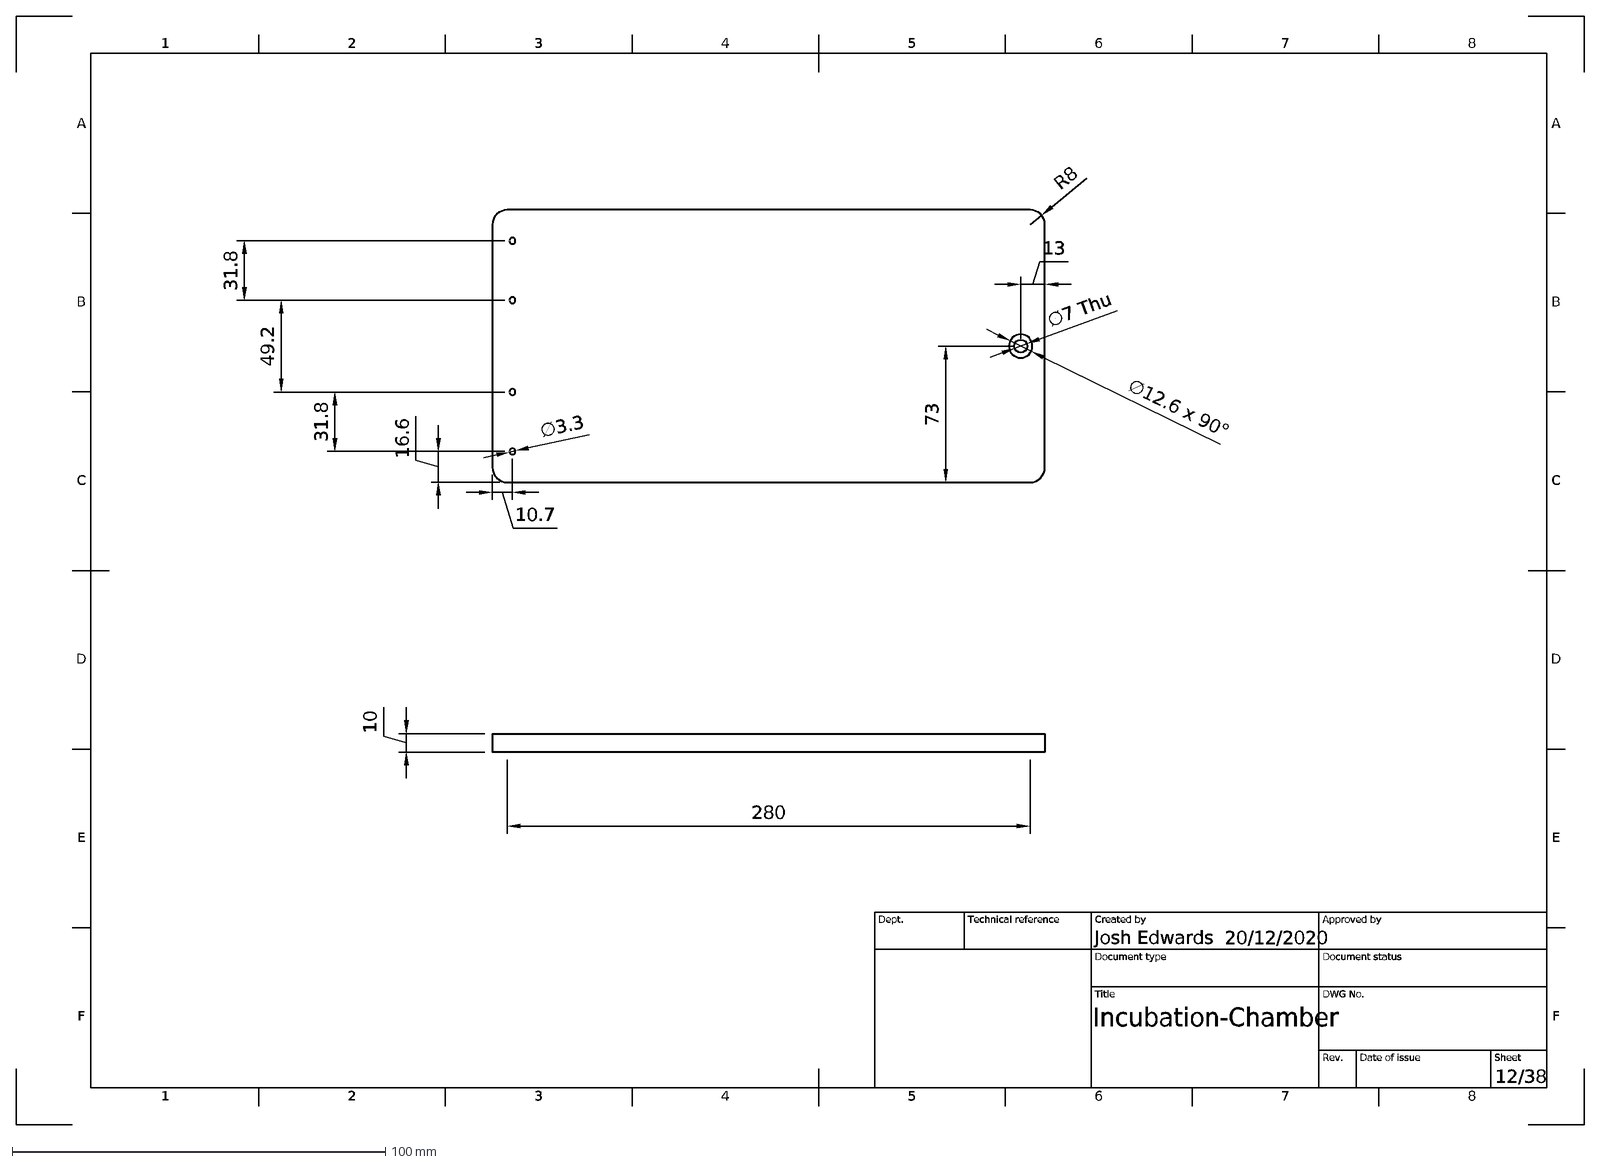
[picture p65: CAD file, 2020-12-22]
Incubation Box/Parts/Incubation-Chamber-Front-Middle-Door.dxf
1
A
2
3
4
5
6
7
8
B
C
D
E
F
20/12/2020
12/38
Incubation-Chamber
Josh Edwards
Dept.
Technical reference
Created by
Approved by
Document type
Document status
Title
DWG No.
Rev.
Date of issue
Sheet
280
10
R8
∅12.6 x 90°
∅7 Thu
13
73
∅3.3
16.6
10.7
31.8
49.2
