HoldenLab/LifeHack/Incubation Box/Parts/Incubation-Chamber-Top-Diffuser-Mount.dxf

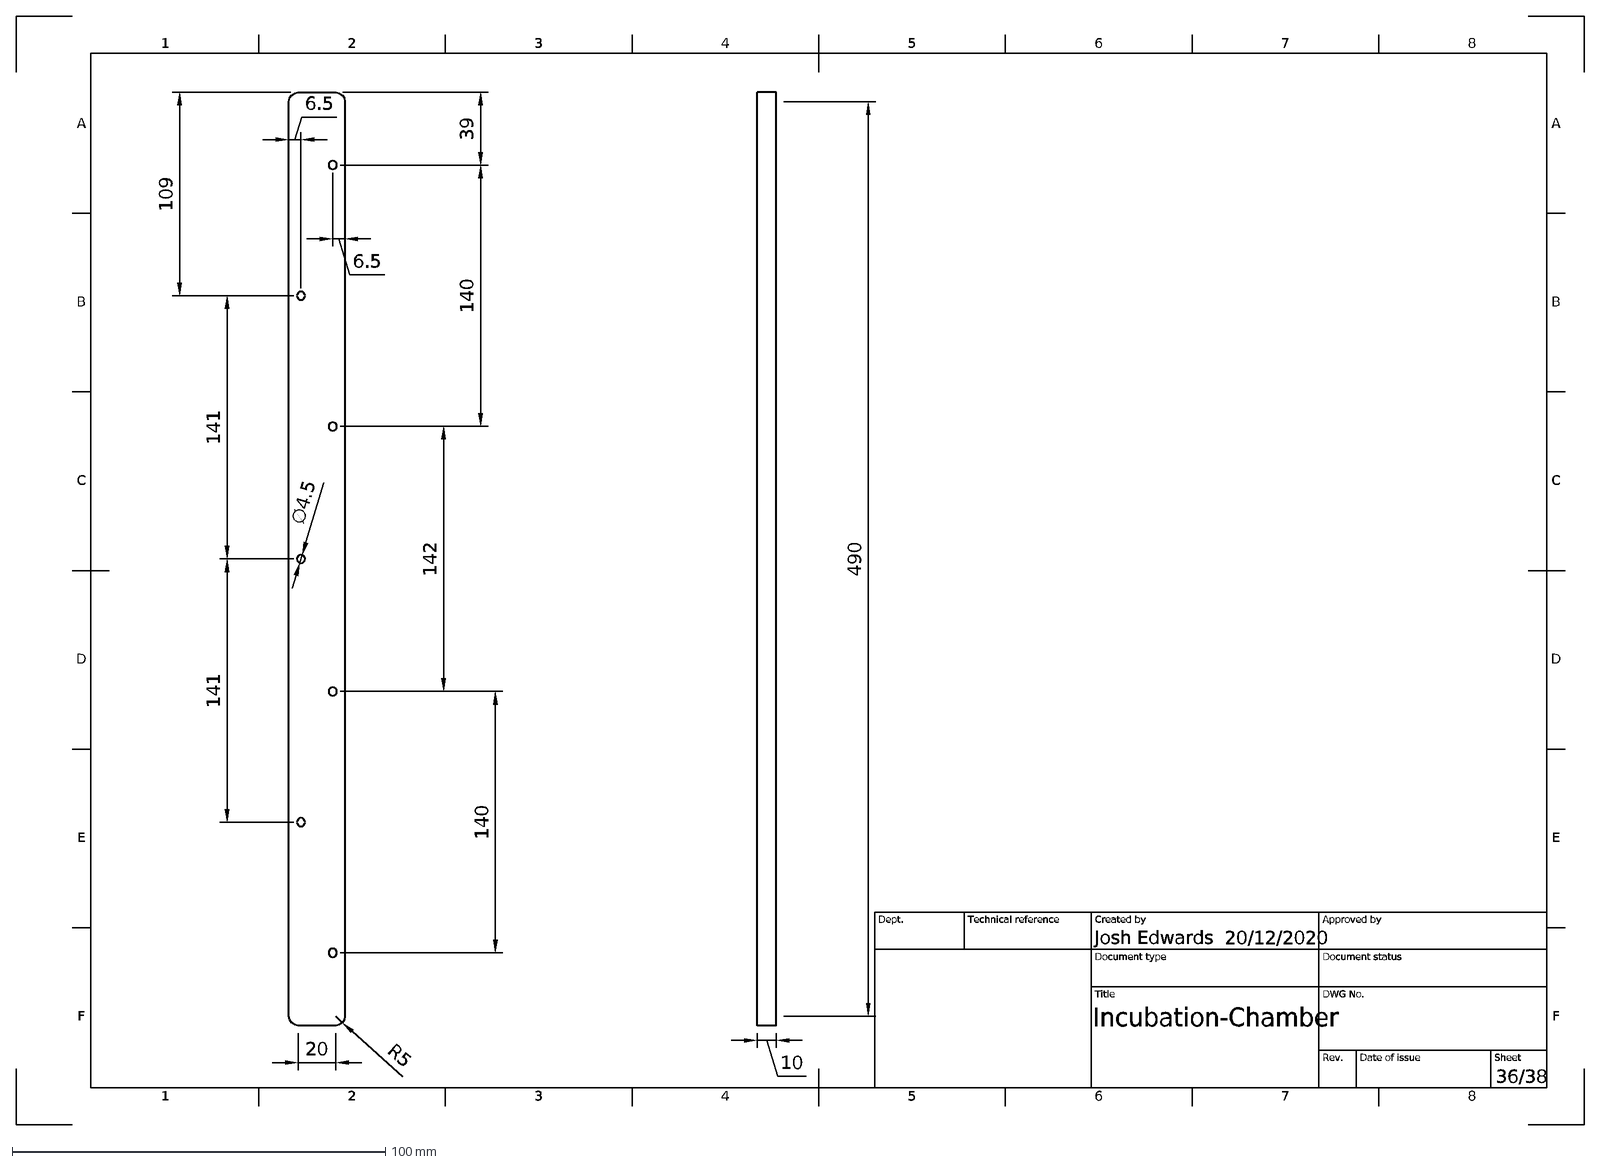
[picture p66: CAD file, 2020-12-22]
Incubation Box/Parts/Incubation-Chamber-Top-Diffuser-Mount.dxf
1
A
2
3
4
5
6
7
8
B
C
D
E
F
20/12/2020
36/38
Incubation-Chamber
Josh Edwards
Dept.
Technical reference
Created by
Approved by
Document type
Document status
Title
DWG No.
Rev.
Date of issue
Sheet
490
10
R5
20
39
6.5
109
141
140
142
∅4.5
