HoldenLab/LifeHack/Incubation Box/Parts/Incubation-Chamber-Back-Access-Hatch.dxf

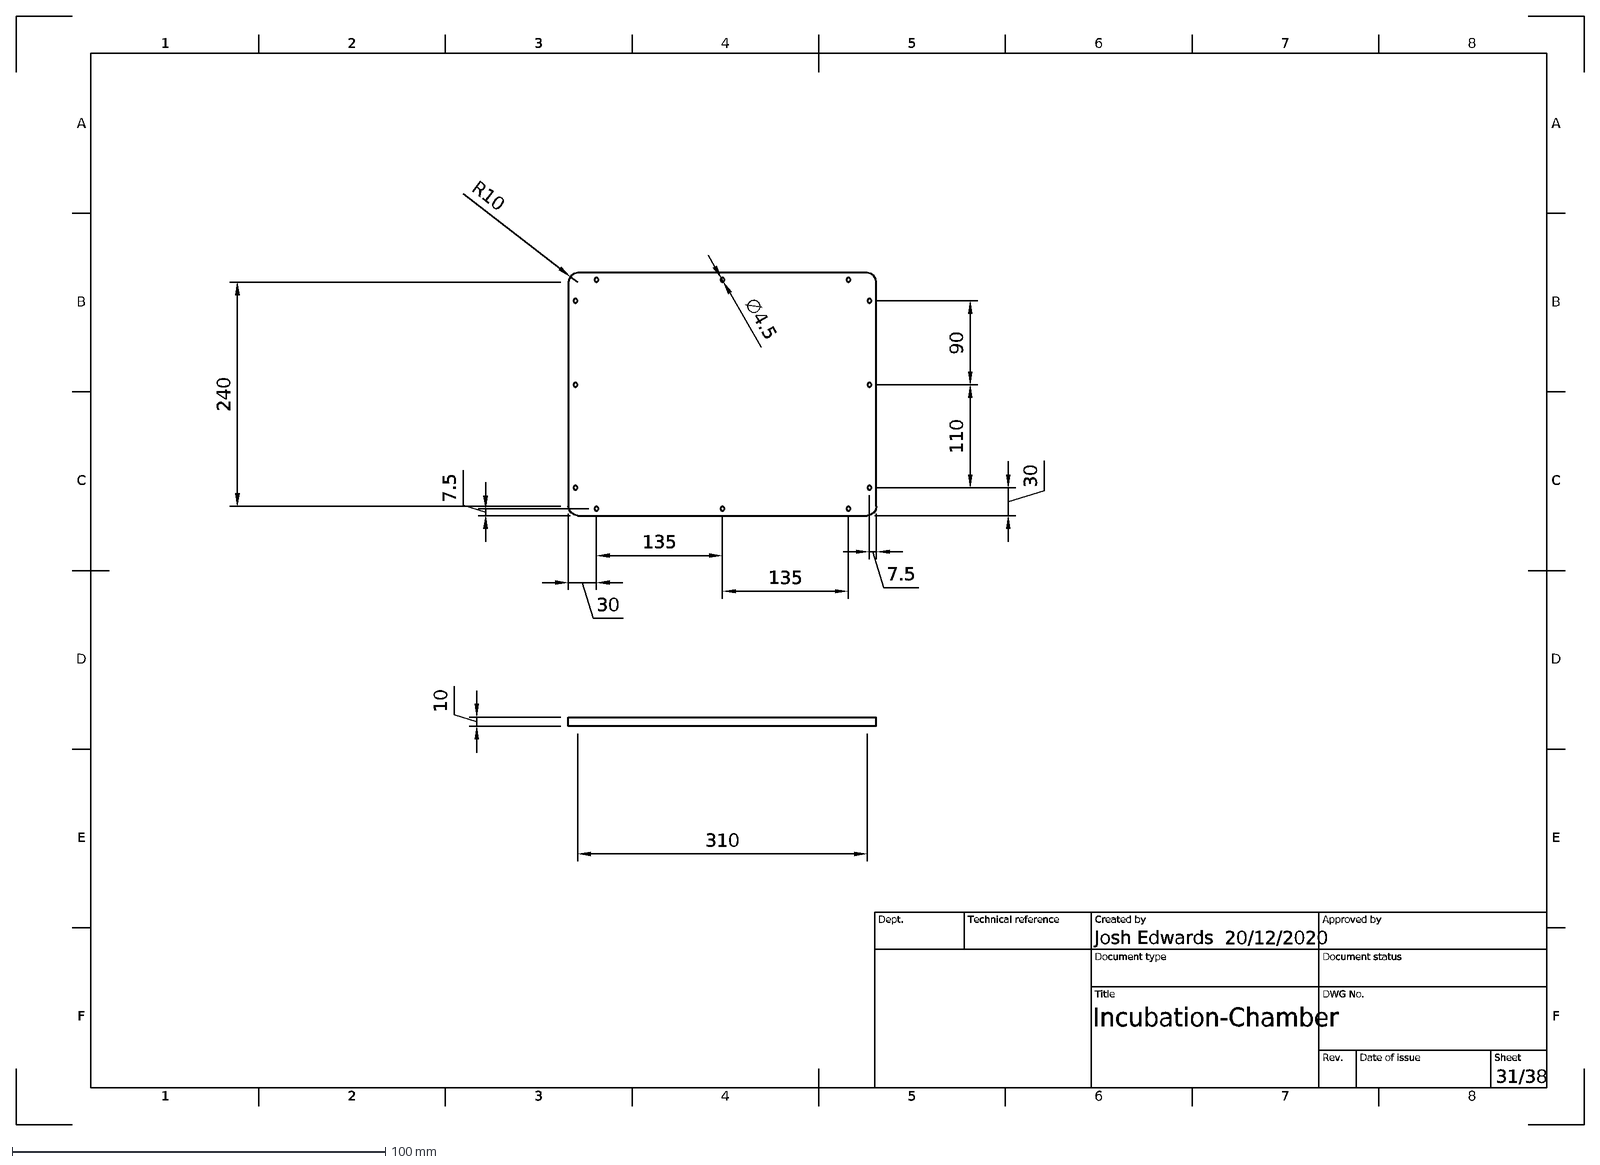
[picture p67: CAD file, 2020-12-22]
Incubation Box/Parts/Incubation-Chamber-Back-Access-Hatch.dxf
1
A
2
3
4
5
6
7
8
B
C
D
E
F
20/12/2020
31/38
Incubation-Chamber
Josh Edwards
Dept.
Technical reference
Created by
Approved by
Document type
Document status
Title
DWG No.
Rev.
Date of issue
Sheet
310
10
240
R10
7.5
30
110
90
∅4.5
135
