HoldenLab/LifeHack/Incubation Box/Parts/Incubation-Chamber-Right-Crisp-Hatch.dxf

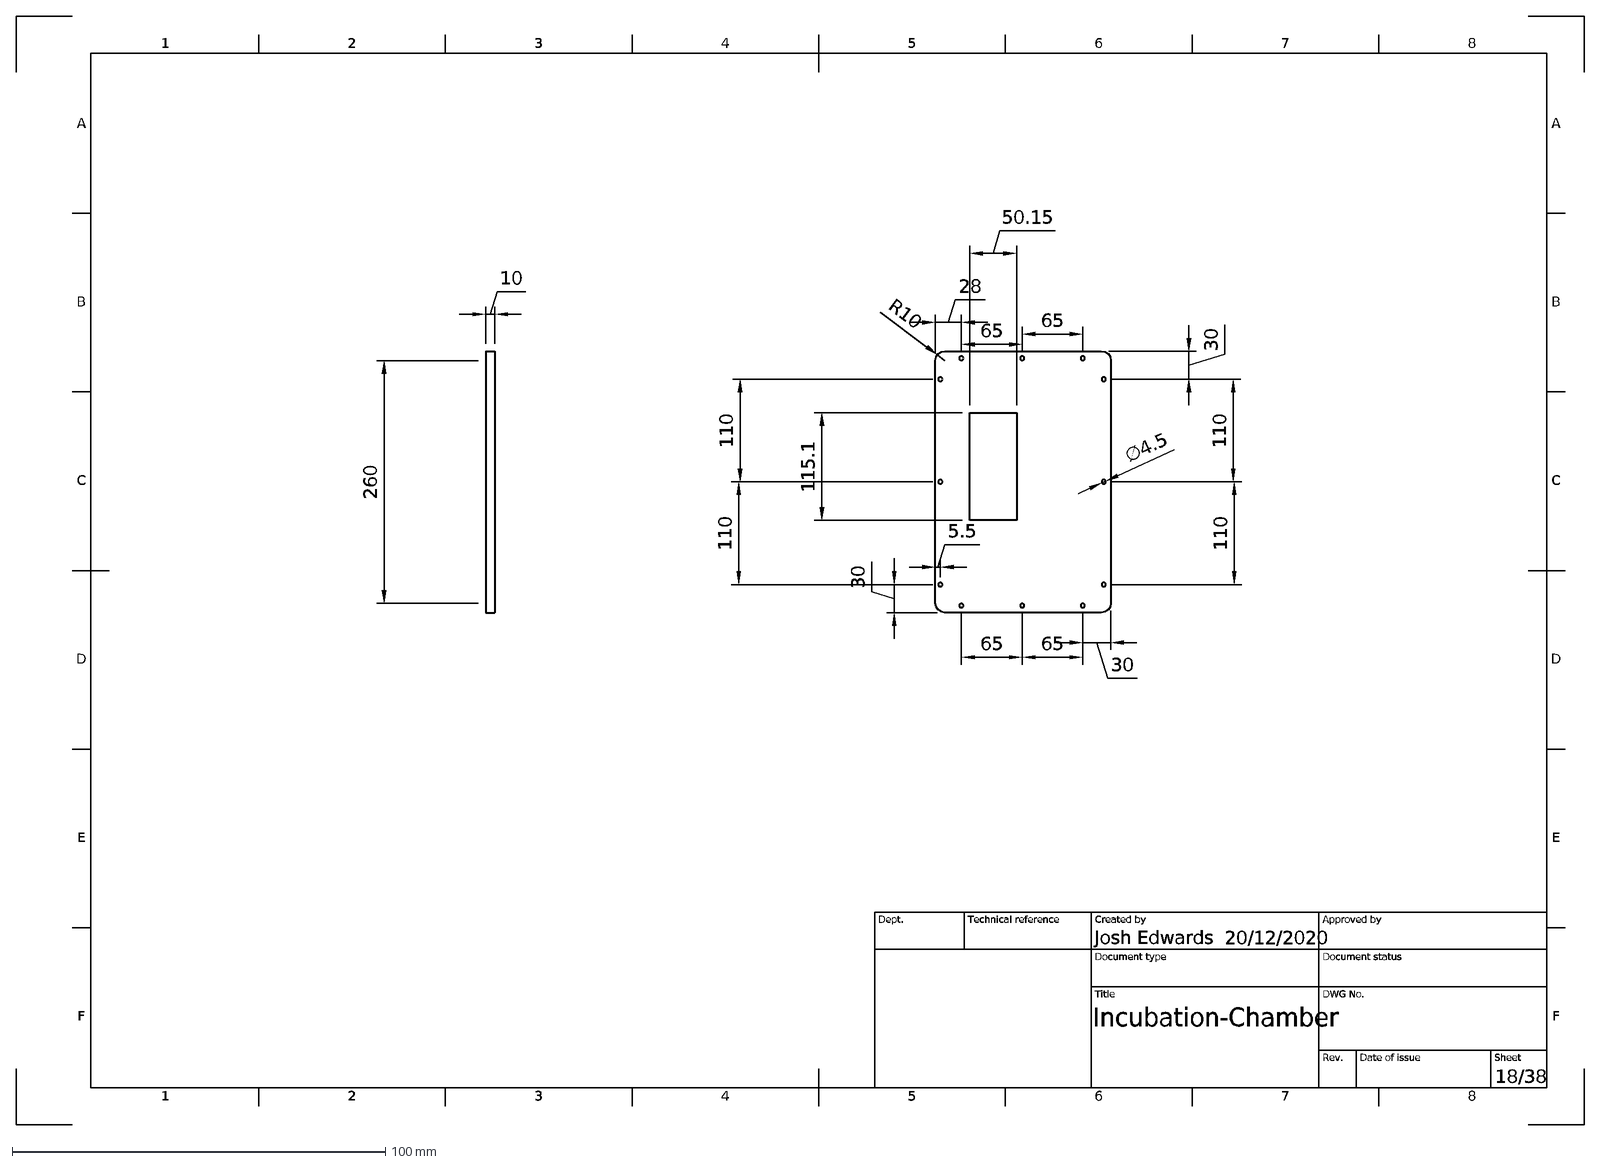
[picture p68: CAD file, 2020-12-22]
Incubation Box/Parts/Incubation-Chamber-Right-Crisp-Hatch.dxf
1
A
2
3
4
5
6
7
8
B
C
D
E
F
20/12/2020
18/38
Incubation-Chamber
Josh Edwards
Dept.
Technical reference
Created by
Approved by
Document type
Document status
Title
DWG No.
Rev.
Date of issue
Sheet
260
10
R10
30
5.5
115.1
50.15
∅4.5
110
28
65
