HoldenLab/LifeHack/Incubation Box/Parts/Incubation-Chamber-Back-Bottom-Heater-Mount.dxf

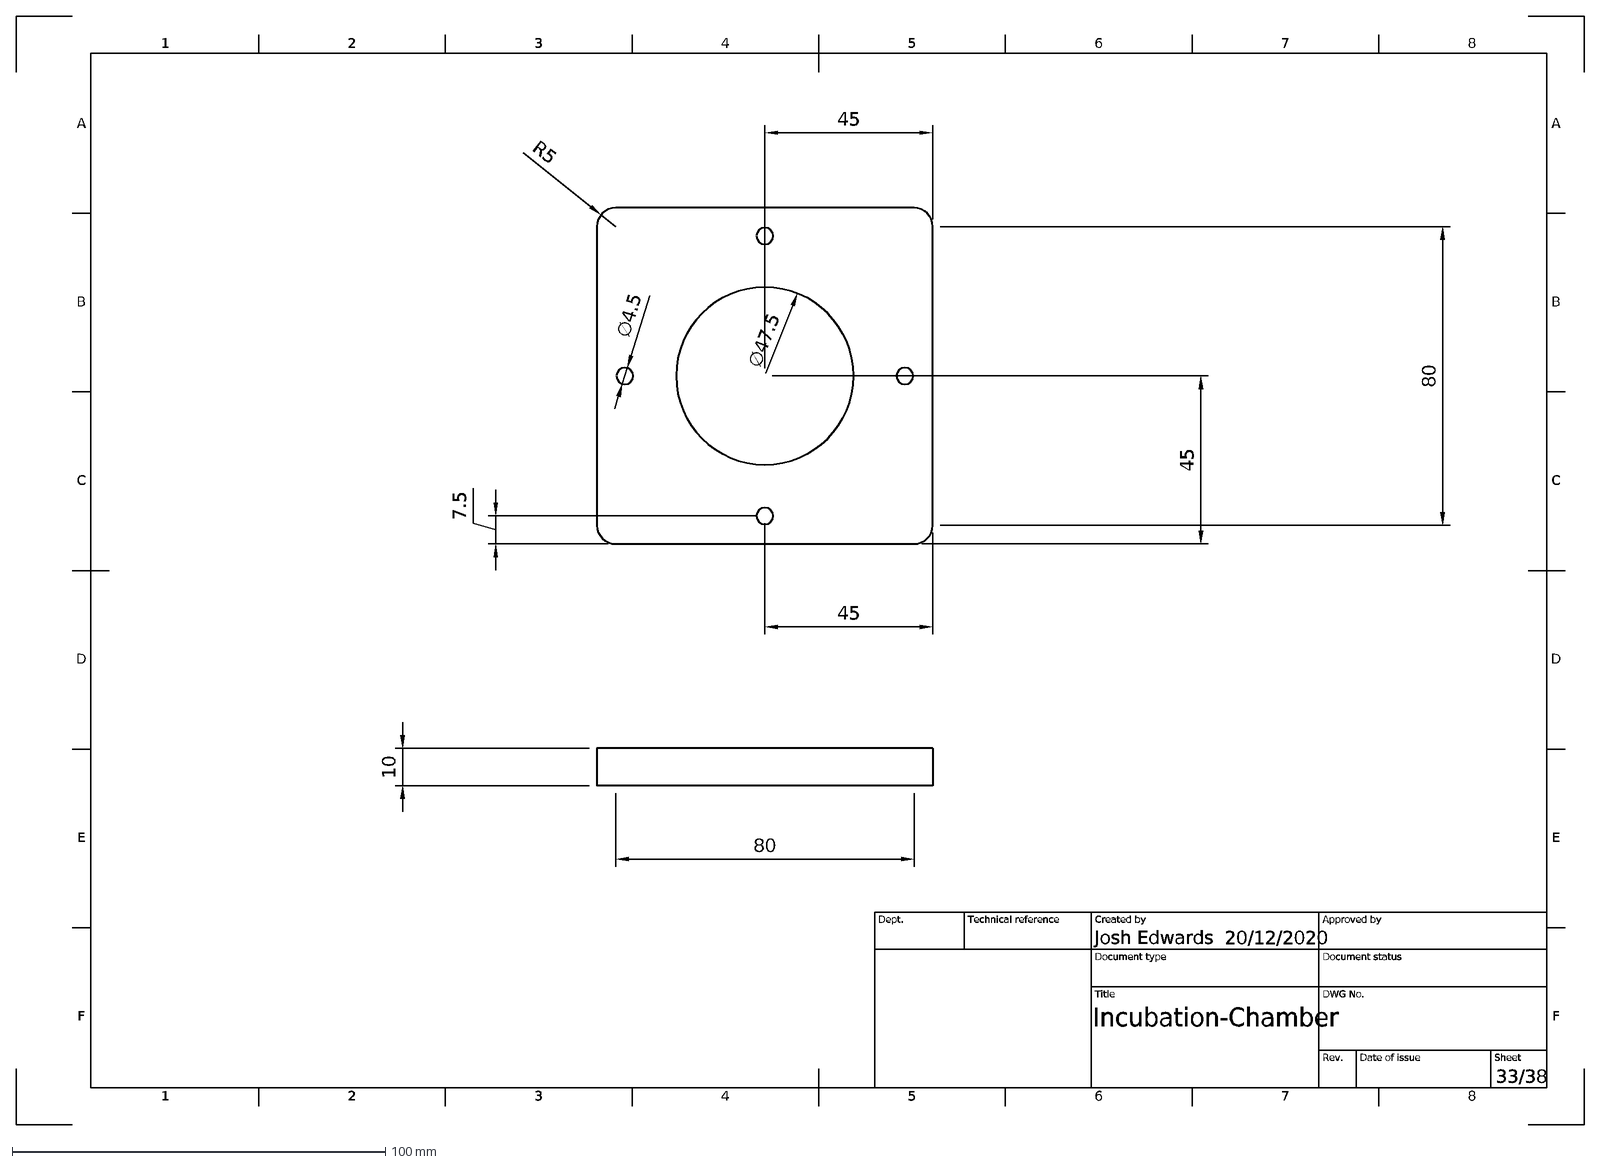
[picture p69: CAD file, 2020-12-22]
Incubation Box/Parts/Incubation-Chamber-Back-Bottom-Heater-Mount.dxf
1
A
2
3
4
5
6
7
8
B
C
D
E
F
20/12/2020
33/38
Incubation-Chamber
Josh Edwards
Dept.
Technical reference
Created by
Approved by
Document type
Document status
Title
DWG No.
Rev.
Date of issue
Sheet
80
10
R5
∅4.5
45
7.5
∅47.5
