HoldenLab/LifeHack/Incubation Box/Parts/Incubation-Chamber-Left-Door.dxf

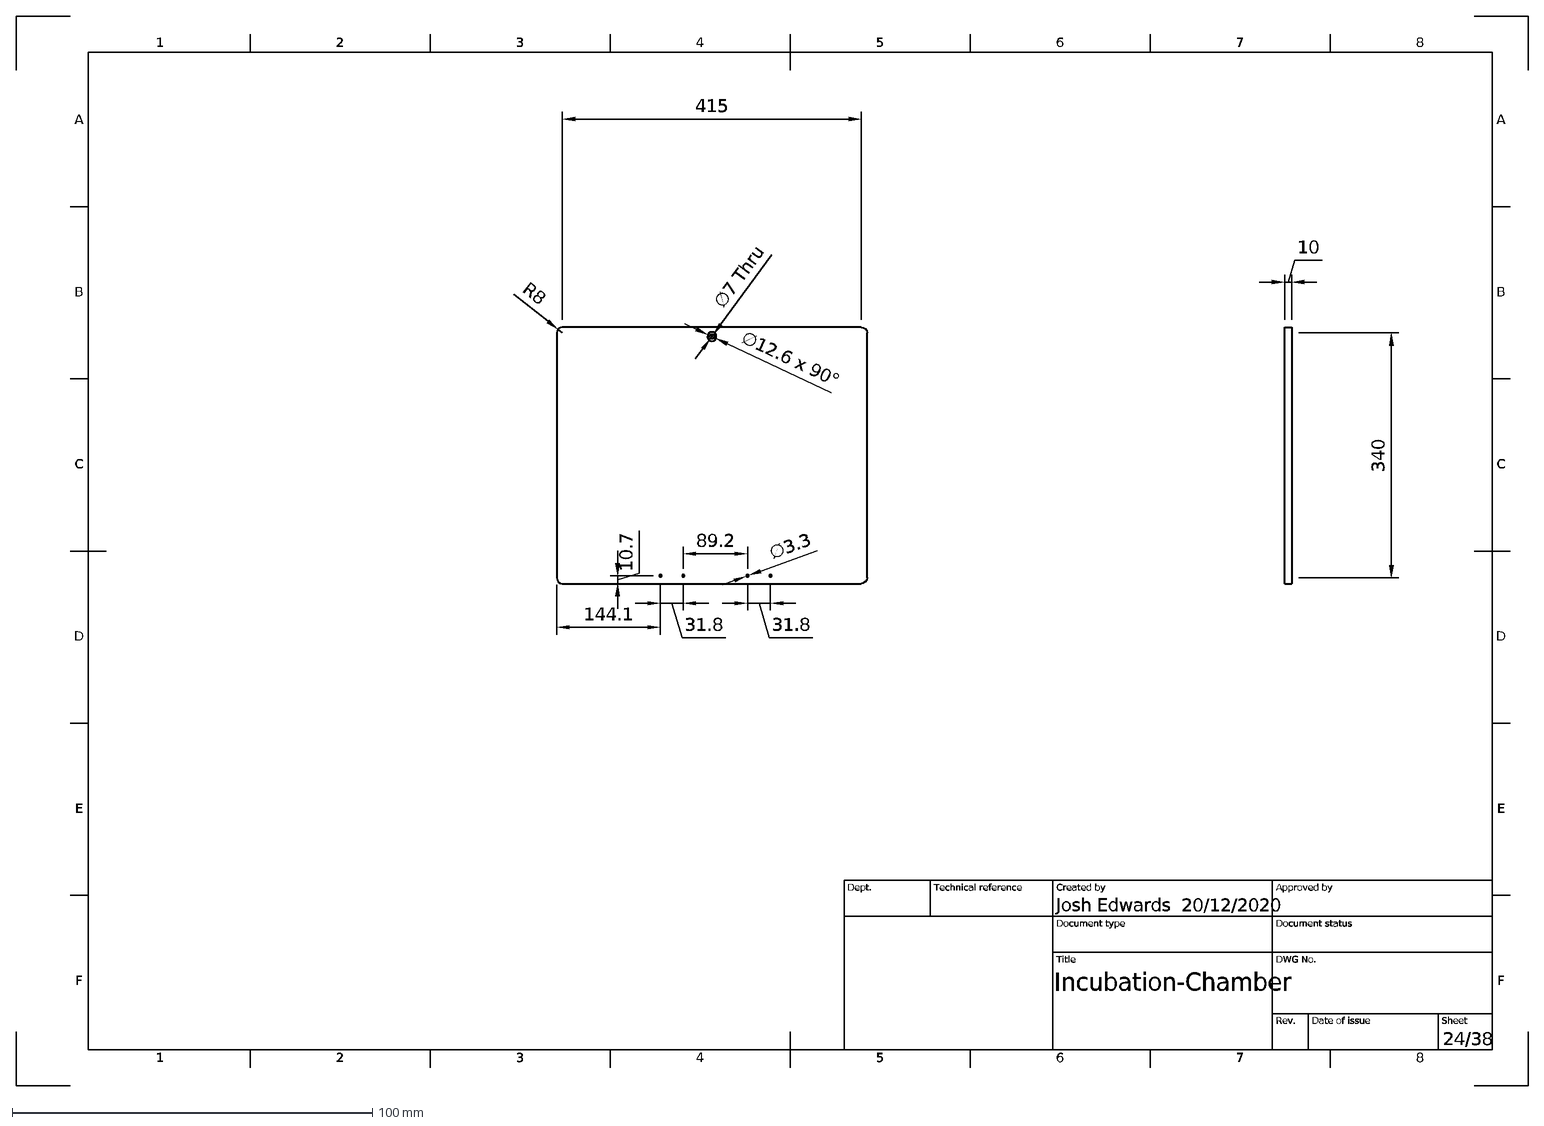
[picture p70: CAD file, 2020-12-22]
Incubation Box/Parts/Incubation-Chamber-Left-Door.dxf
1
A
2
3
4
5
6
7
8
B
C
D
E
F
20/12/2020
24/38
Incubation-Chamber
Josh Edwards
Dept.
Technical reference
Created by
Approved by
Document type
Document status
Title
DWG No.
Rev.
Date of issue
Sheet
340
10
415
∅12.6 x 90°
∅7 Thru
R8
31.8
89.2
144.1
10.7
∅3.3
