HoldenLab/LifeHack/Incubation Box/Parts/Incubation-Chamber-Left-Door-Mount1.dxf

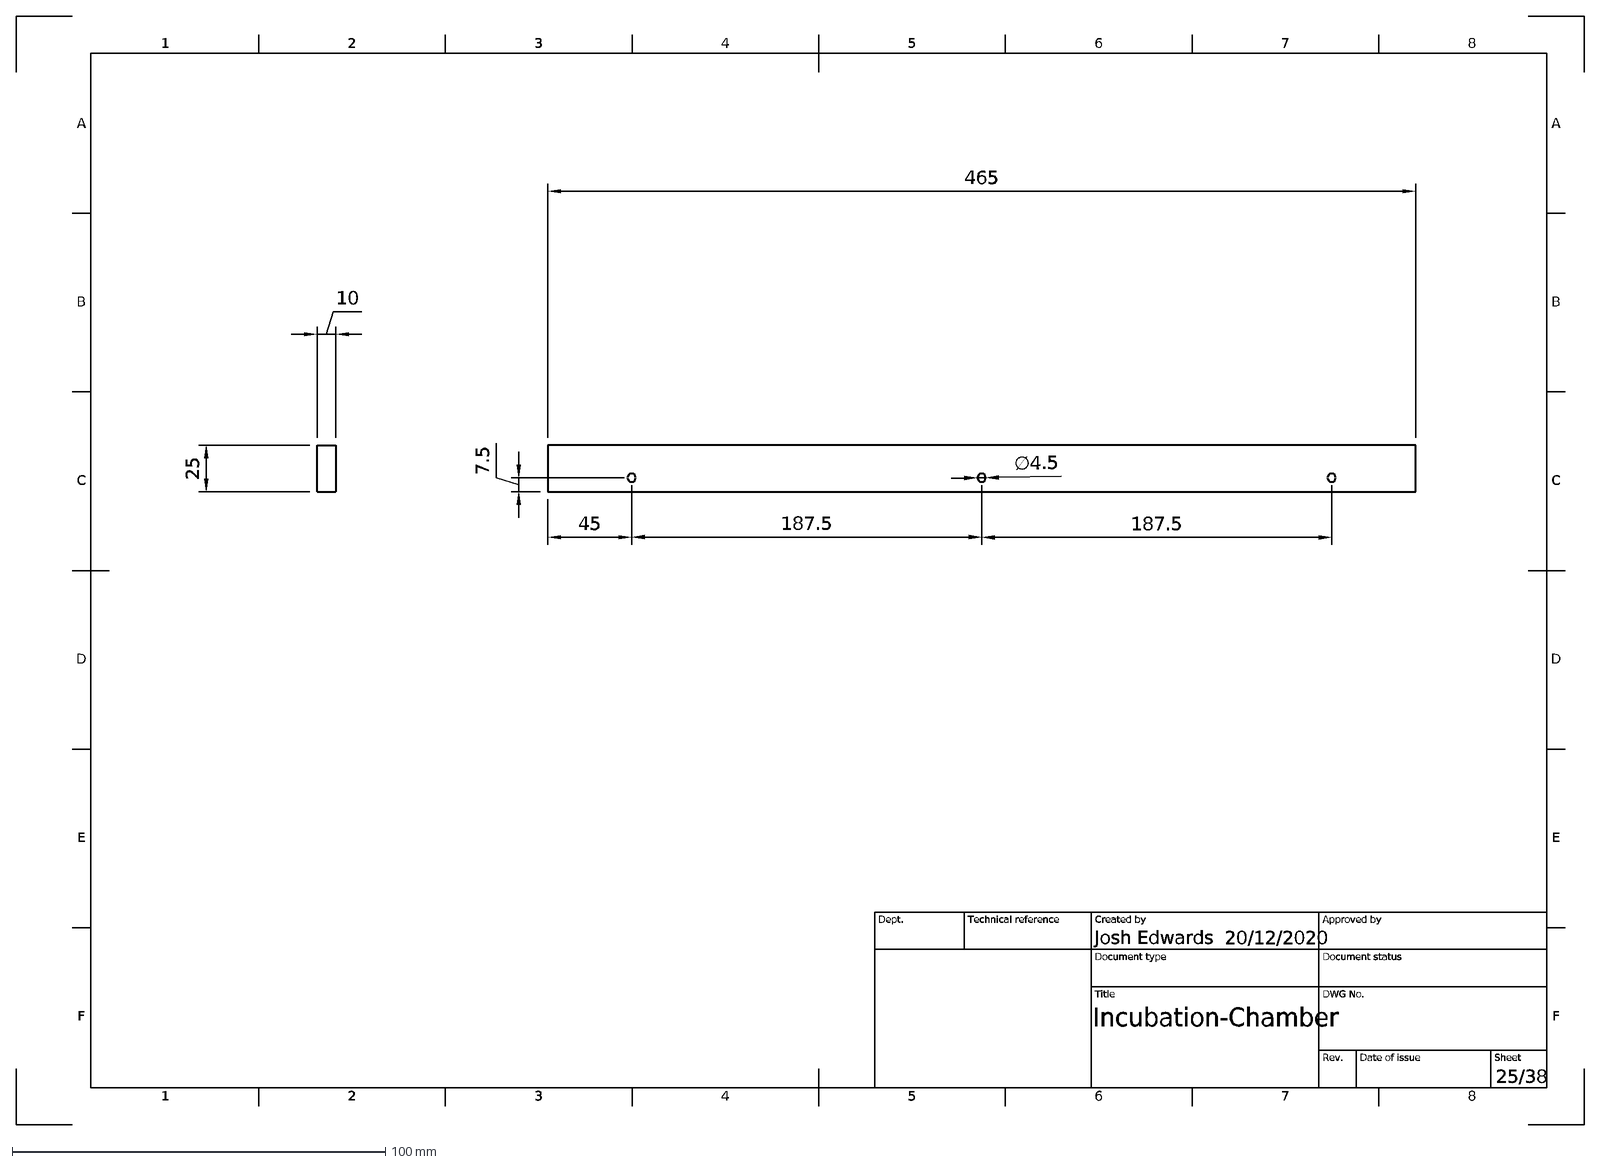
[picture p71: CAD file, 2020-12-22]
Incubation Box/Parts/Incubation-Chamber-Left-Door-Mount1.dxf
1
A
2
3
4
5
6
7
8
B
C
D
E
F
20/12/2020
25/38
Incubation-Chamber
Josh Edwards
Dept.
Technical reference
Created by
Approved by
Document type
Document status
Title
DWG No.
Rev.
Date of issue
Sheet
10
25
465
7.5
45
187.5
∅4.5
