HoldenLab/LifeHack/Incubation Box/Parts/Incubation-Chamber-Front-Window.dxf

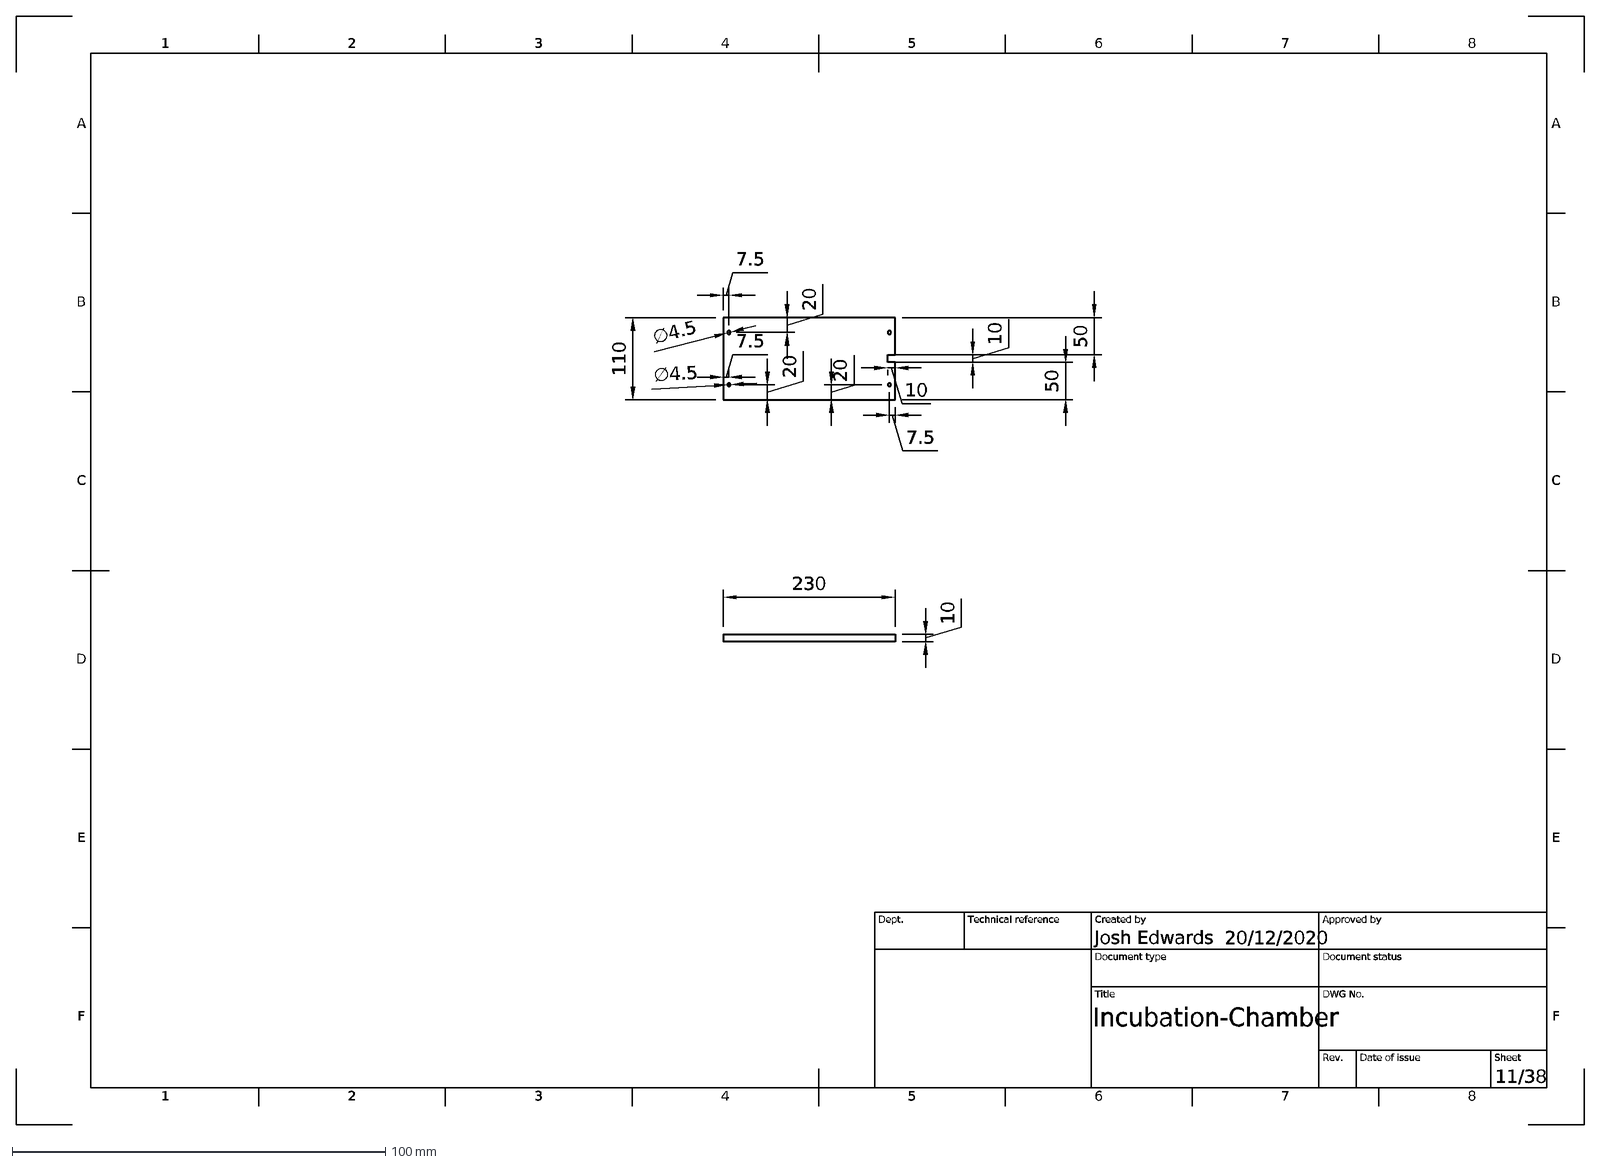
[picture p72: CAD file, 2020-12-22]
Incubation Box/Parts/Incubation-Chamber-Front-Window.dxf
1
A
2
3
4
5
6
7
8
B
C
D
E
F
20/12/2020
11/38
Incubation-Chamber
Josh Edwards
Dept.
Technical reference
Created by
Approved by
Document type
Document status
Title
DWG No.
Rev.
Date of issue
Sheet
230
10
110
50
7.5
20
∅4.5
