HoldenLab/LifeHack/Incubation Box/Parts/Incubation-Chamber-Back-Panel.dxf

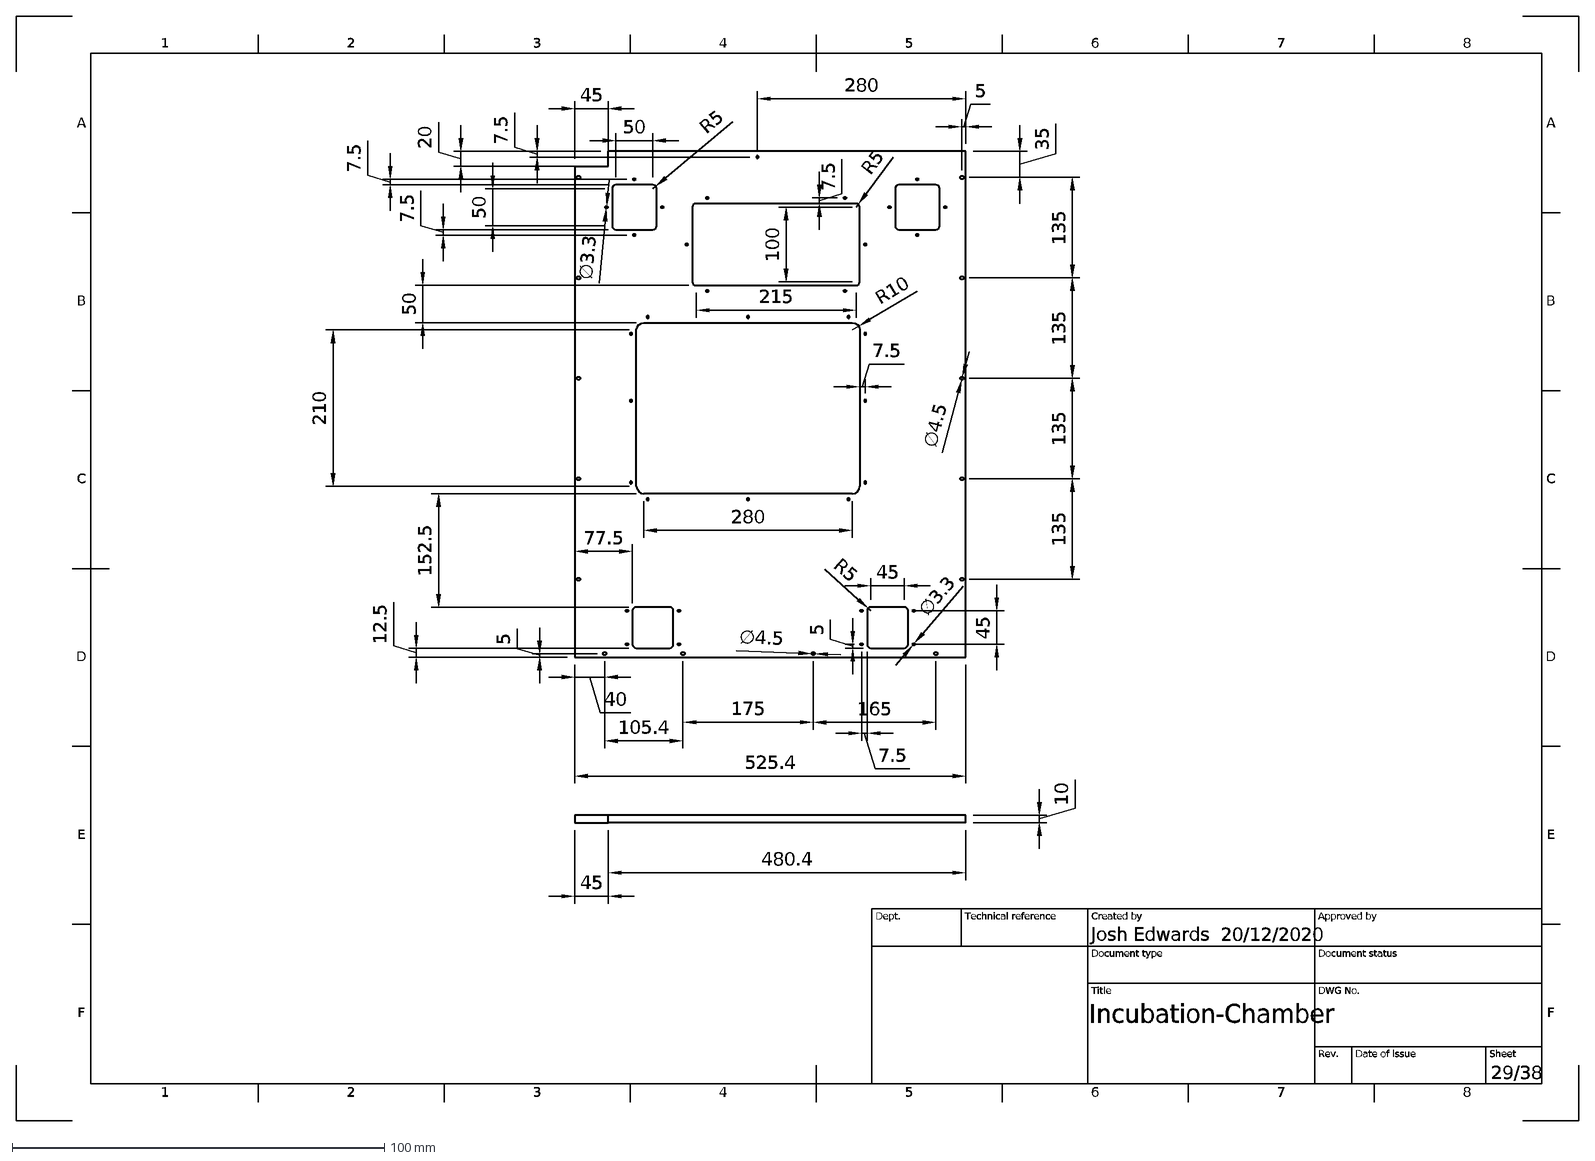
[picture p73: CAD file, 2020-12-22]
Incubation Box/Parts/Incubation-Chamber-Back-Panel.dxf
1
A
2
3
4
5
6
7
8
B
C
D
E
F
20/12/2020
29/38
Incubation-Chamber
Josh Edwards
Dept.
Technical reference
Created by
Approved by
Document type
Document status
Title
DWG No.
Rev.
Date of issue
Sheet
480.4
45
10
525.4
40
105.4
175
165
∅4.5
R5
7.5
∅3.3
20
35
135
77.5
12.5
280
152.5
50
210
215
100
R10
