HoldenLab/LifeHack/Incubation Box/Parts/Incubation-Chamber-Top-Panel.dxf

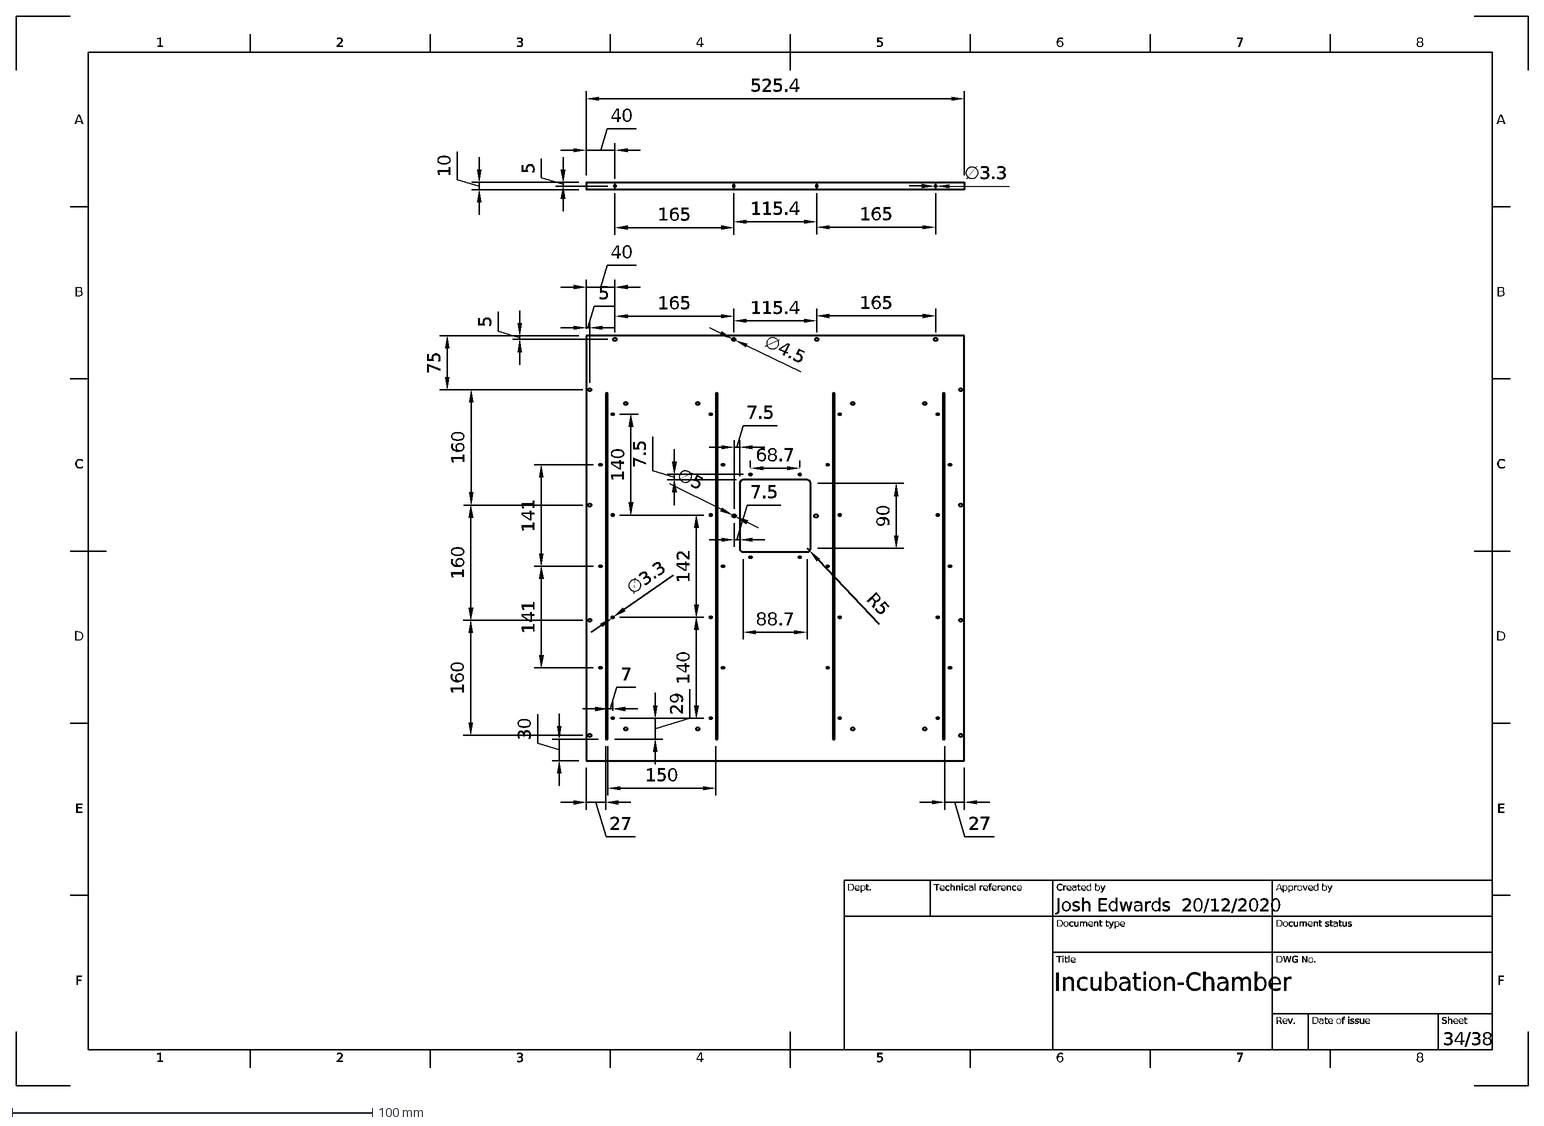
[picture p74: CAD file, 2020-12-22]
Incubation Box/Parts/Incubation-Chamber-Top-Panel.dxf
1
A
2
3
4
5
6
7
8
B
C
D
E
F
20/12/2020
34/38
Incubation-Chamber
Josh Edwards
Dept.
Technical reference
Created by
Approved by
Document type
Document status
Title
DWG No.
Rev.
Date of issue
Sheet
10
525.4
40
165
115.4
∅4.5
∅3.3
75
160
27
30
29
141
140
142
150
88.7
90
R5
∅5
7.5
68.7
