HoldenLab/LifeHack/Incubation Box/Parts/Incubation-Chamber-Back-Top-Heater-Mount.dxf

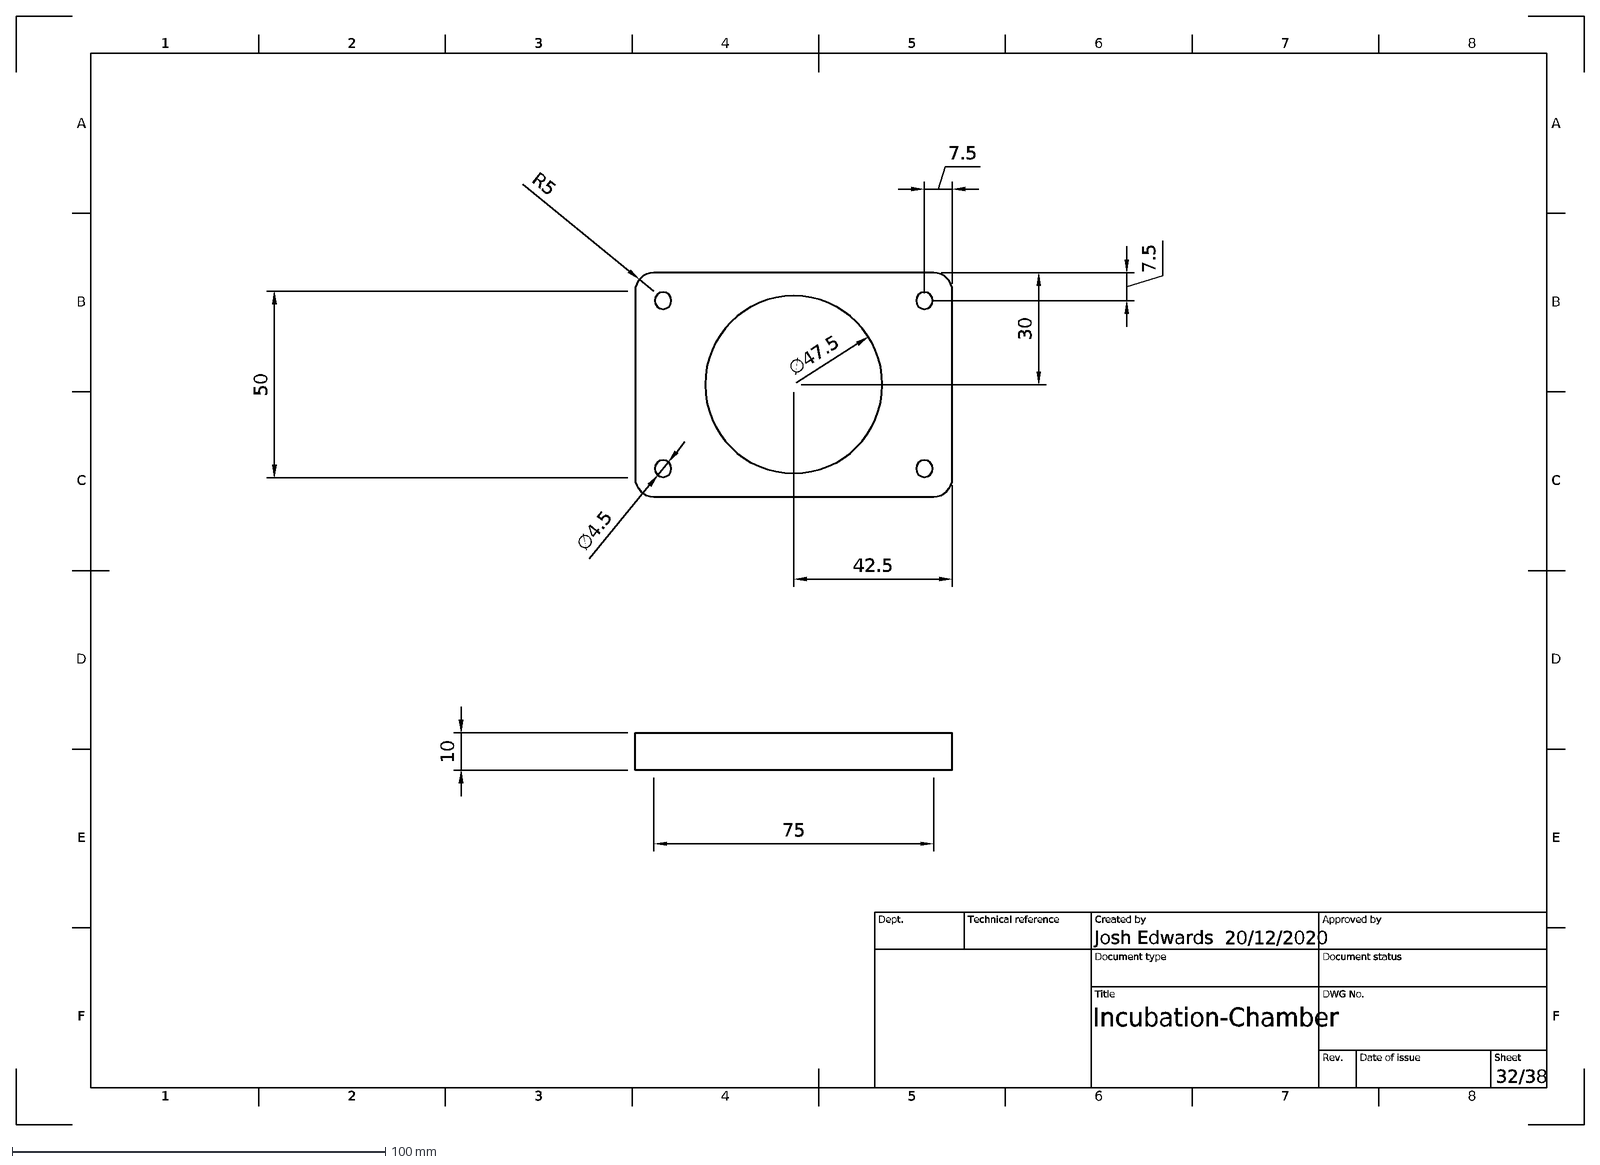
[picture p75: CAD file, 2020-12-22]
Incubation Box/Parts/Incubation-Chamber-Back-Top-Heater-Mount.dxf
1
A
2
3
4
5
6
7
8
B
C
D
E
F
20/12/2020
32/38
Incubation-Chamber
Josh Edwards
Dept.
Technical reference
Created by
Approved by
Document type
Document status
Title
DWG No.
Rev.
Date of issue
Sheet
75
10
50
∅4.5
R5
7.5
42.5
30
∅47.5
