HoldenLab/LifeHack/Incubation Box/Parts/Incubation-Chamber-Right-Door-Mount2.dxf

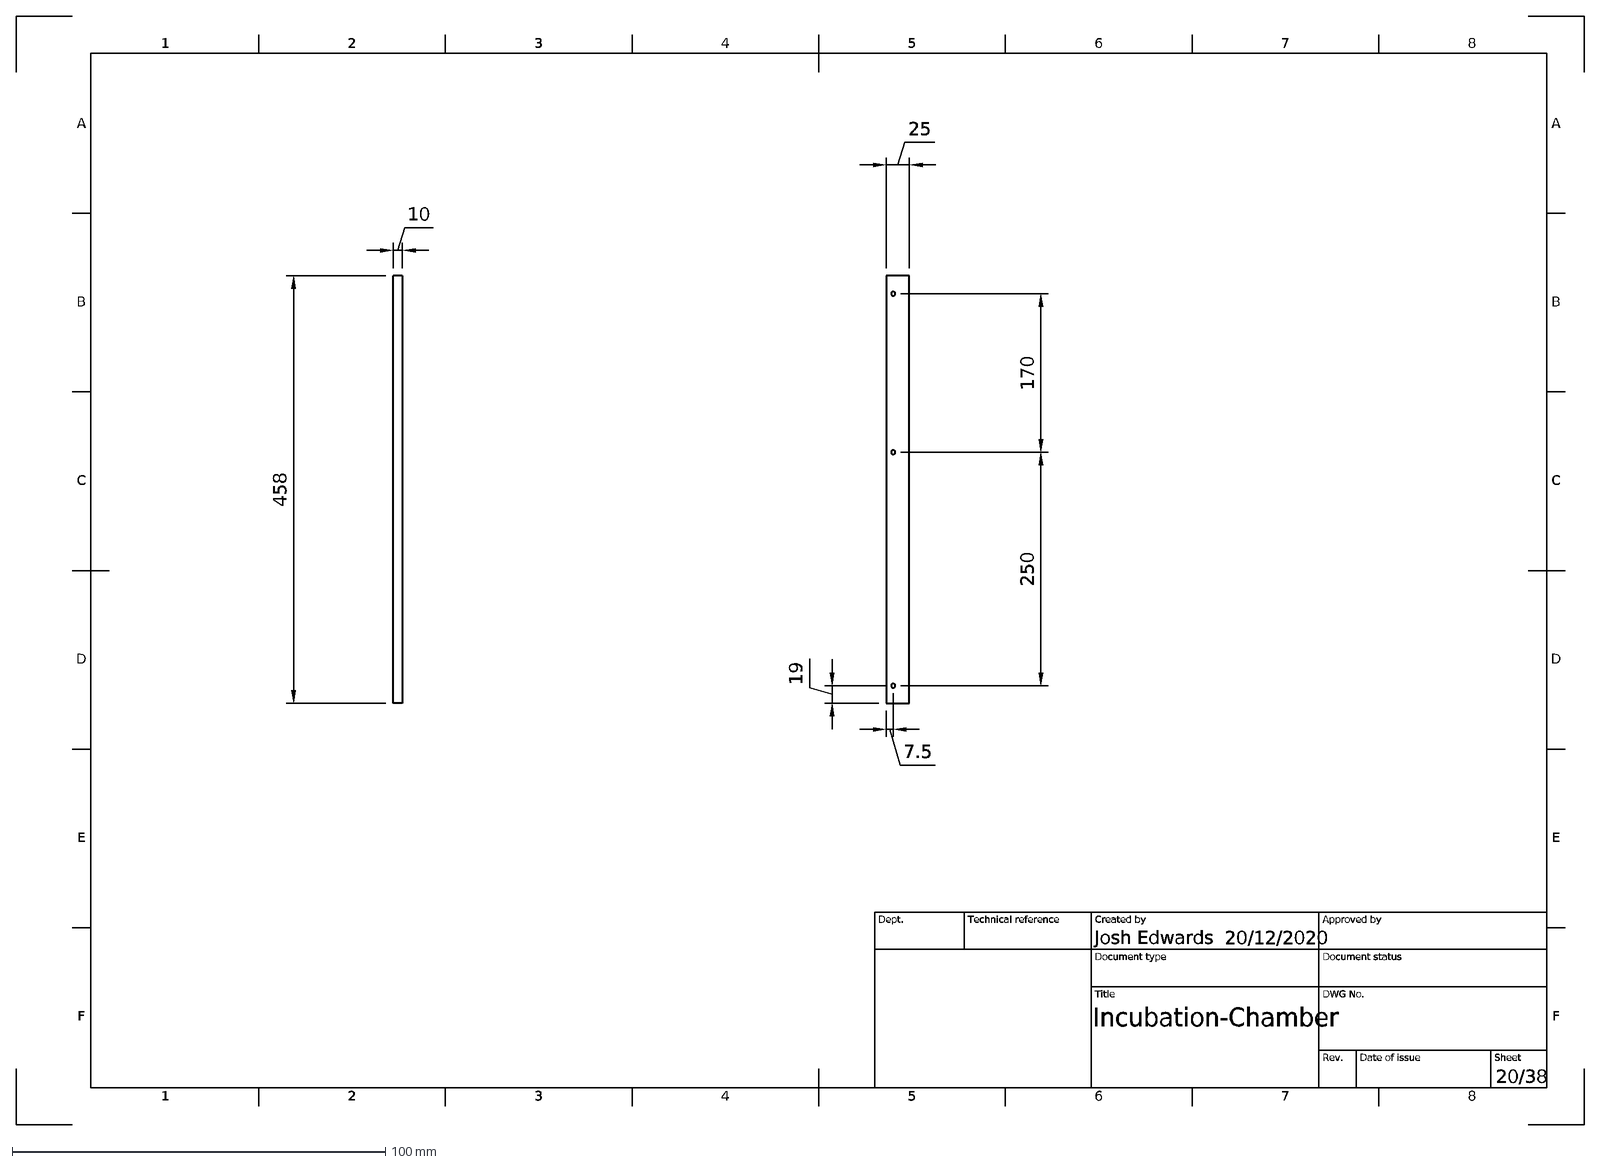
[picture p76: CAD file, 2020-12-22]
Incubation Box/Parts/Incubation-Chamber-Right-Door-Mount2.dxf
1
A
2
3
4
5
6
7
8
B
C
D
E
F
20/12/2020
20/38
Incubation-Chamber
Josh Edwards
Dept.
Technical reference
Created by
Approved by
Document type
Document status
Title
DWG No.
Rev.
Date of issue
Sheet
10
458
25
19
7.5
250
170
